Engineerabot/Cheetah/modelio/Raza/doc/hi/img/c8a9e4ff-c5fc-48f4-94d7-1af237ac6b6f.png

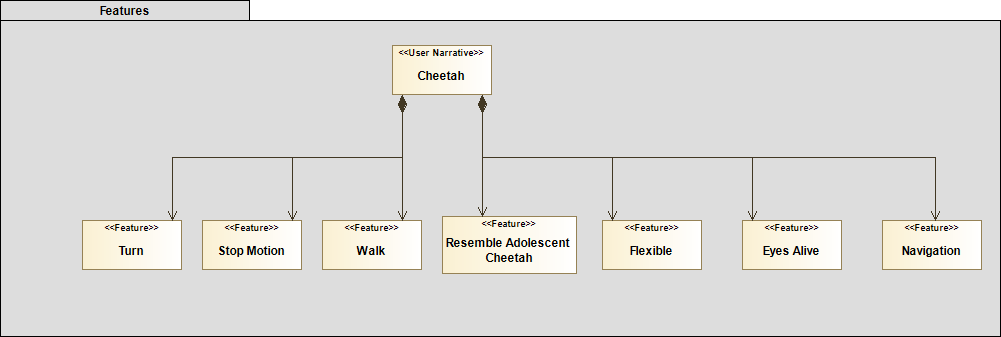
modelio/Raza/doc/hi/img/c8a9e4ff-c5fc-48f4-94d7-1af237ac6b6f.png
