Engineerabot/Cheetah/modelio/Raza/doc/structure/img/92a80e28-67f9-4ed8-8f8e-a8a12a4f9ef7.png

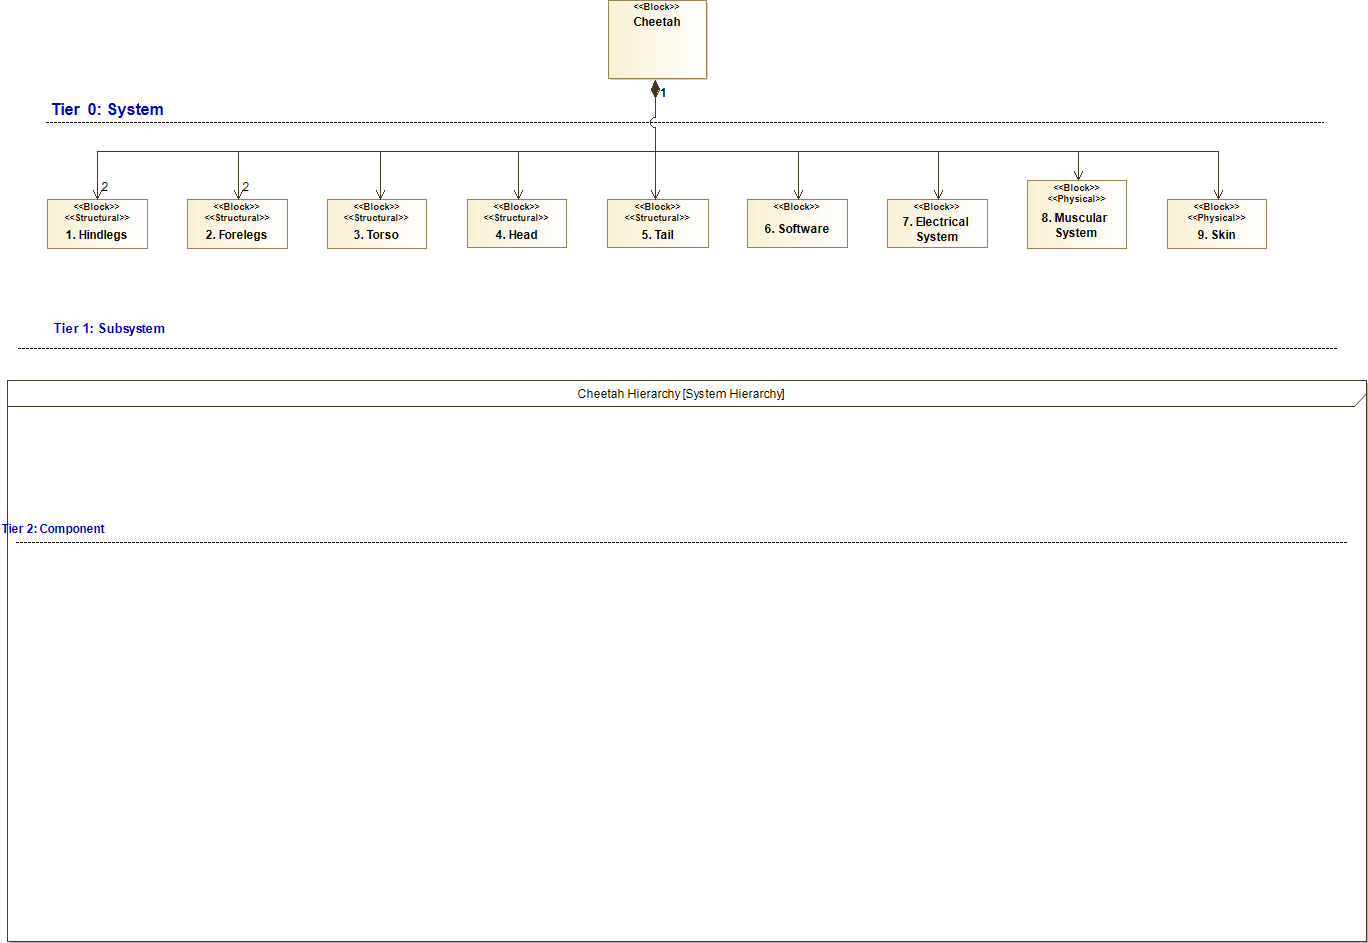
modelio/Raza/doc/structure/img/92a80e28-67f9-4ed8-8f8e-a8a12a4f9ef7.png
