Engineerabot/Cheetah/modelio/Raza/doc/structure/img/a2c1a67e-7b9c-40e4-80ca-a07e13e1c975.png

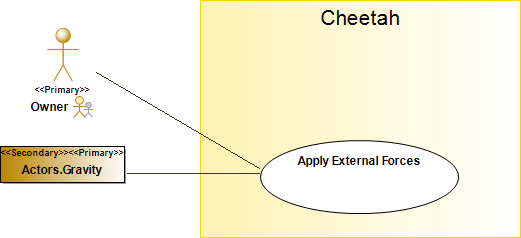
modelio/Raza/doc/structure/img/a2c1a67e-7b9c-40e4-80ca-a07e13e1c975.png
