Engineerabot/Cheetah/manucture/STL/Outer Knee Joint - Left.STL

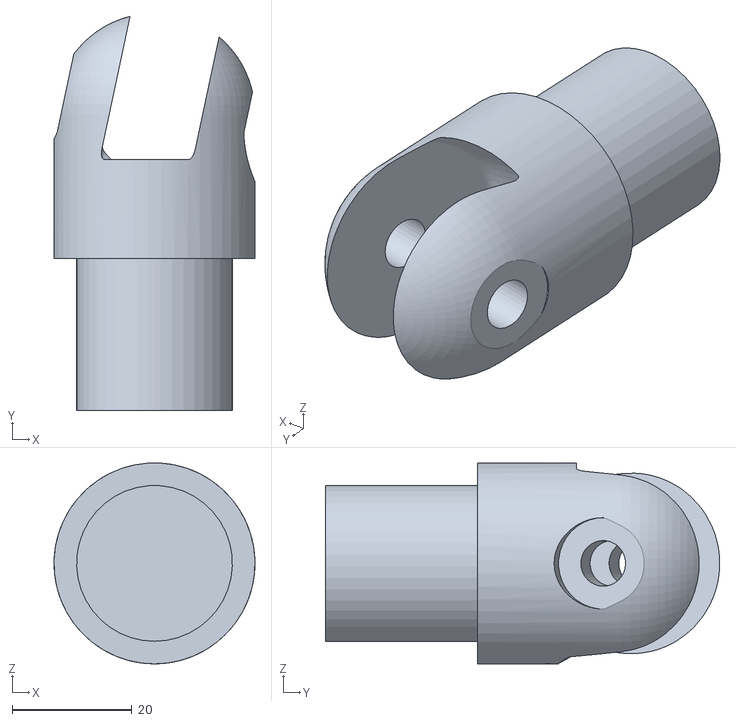
[picture p23: CAD file, 2023-09-10]
manucture/STL/Outer Knee Joint - Left.STL
33.5 x 65.8 x 33.5
