Engineerabot/Cheetah/design/Level 4/Knee Joint Pad.SLDPRT

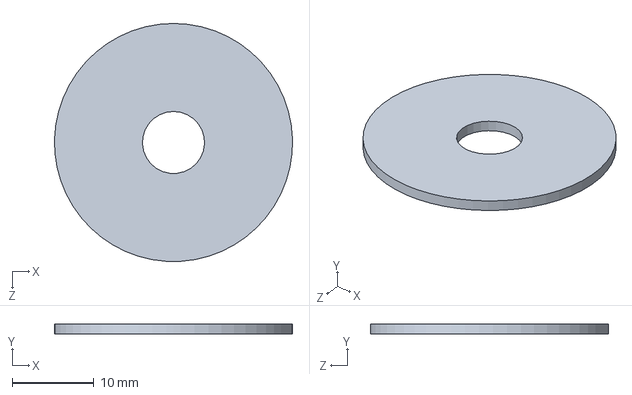
[picture p24: CAD file, 2023-09-10]
design/Level 4/Knee Joint Pad.SLDPRT
29.2 x 1.27 x 29.2 mm
