Engineerabot/Cheetah/manucture/STL/Inner Torso Joint.STL

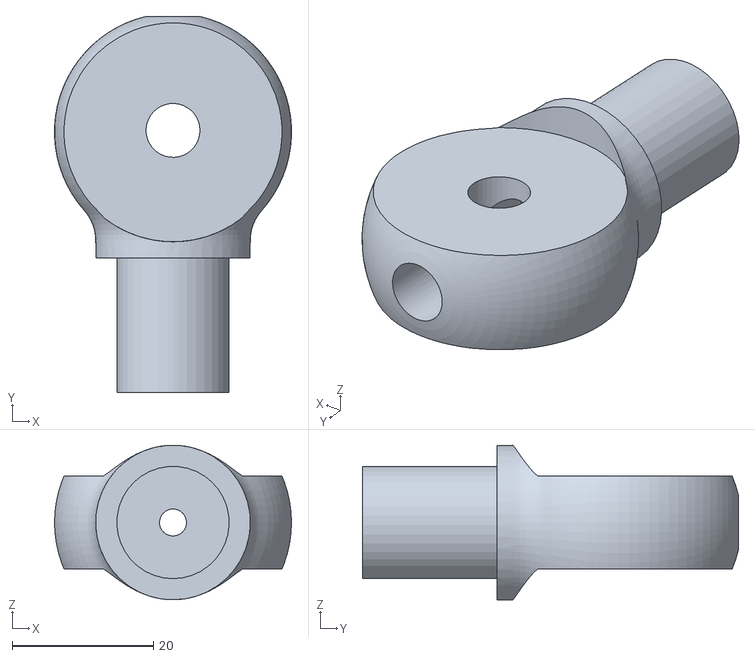
[picture p25: CAD file, 2023-09-10]
manucture/STL/Inner Torso Joint.STL
33.5 x 53.2 x 21.8
