Engineerabot/Cheetah/design/Level 4/Rib7.SLDPRT

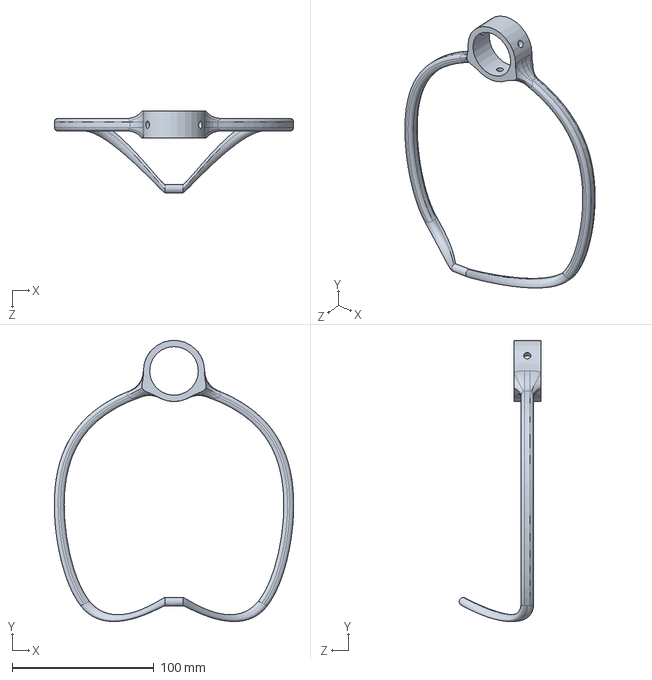
[picture p26: CAD file, 2023-09-10]
design/Level 4/Rib7.SLDPRT
168.7 x 198.0 x 57.5 mm
