Engineerabot/Cheetah/manucture/STL/Outer Elbow Joint.STL

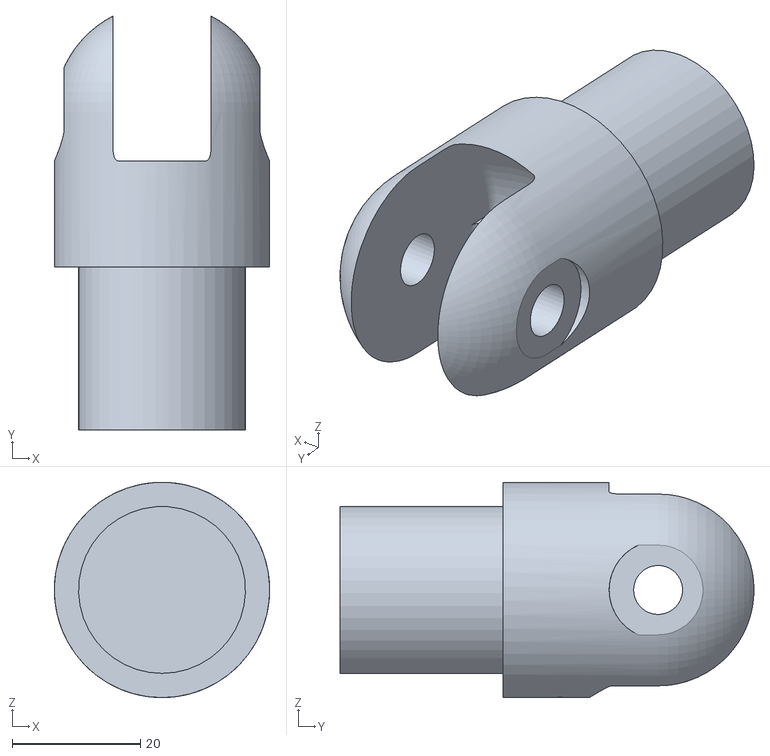
[picture p27: CAD file, 2023-09-10]
manucture/STL/Outer Elbow Joint.STL
33.5 x 64.5 x 33.5
