Engineerabot/Cheetah/design/Level 5/1302-0032-0025-motor mount.SLDPRT

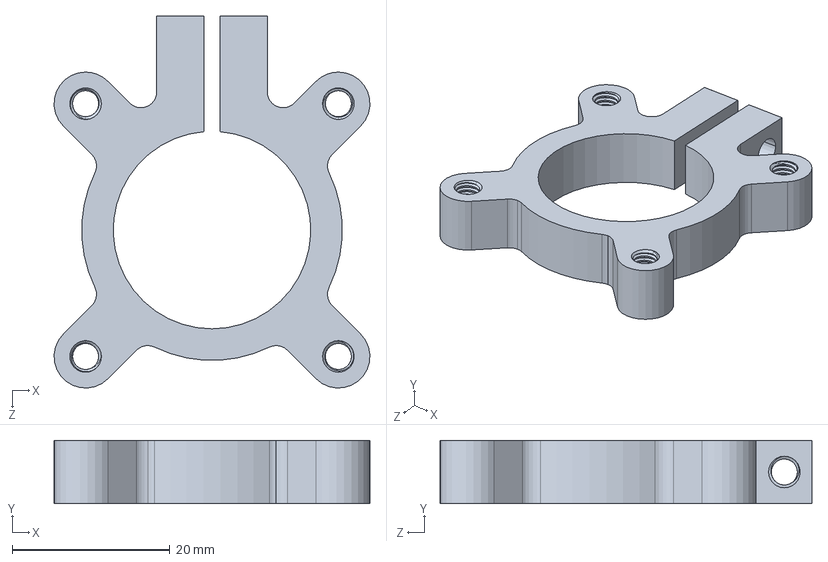
[picture p28: CAD file, 2023-09-10]
design/Level 5/1302-0032-0025-motor mount.SLDPRT
40.0 x 8.00 x 47.1 mm
