Engineerabot/Cheetah/manucture/STL/Inner Knee Joint.STL

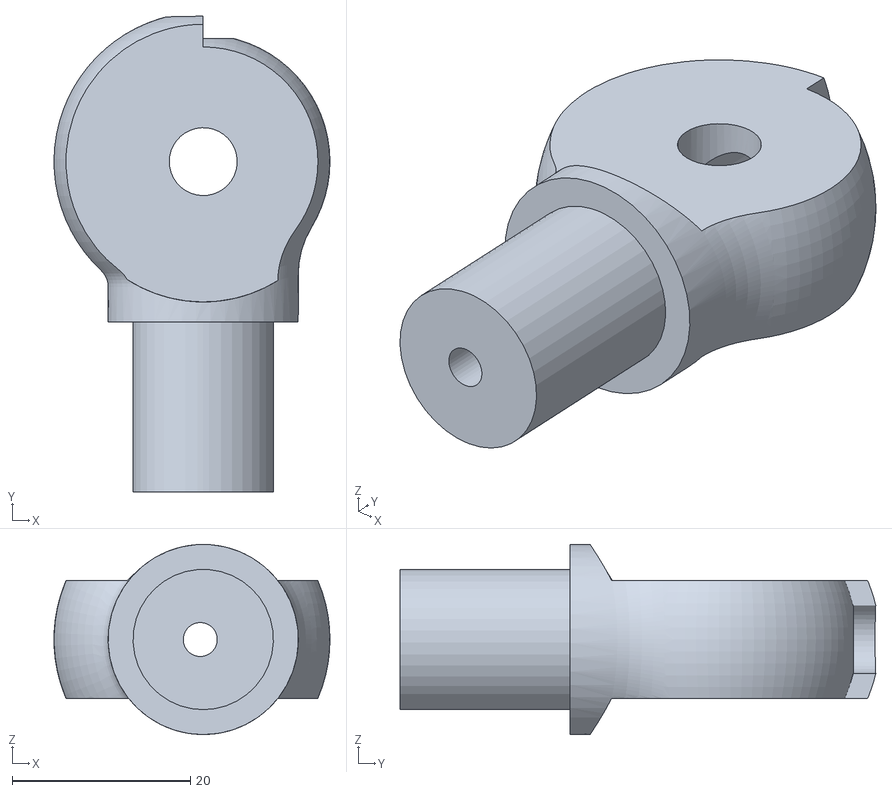
[picture p29: CAD file, 2022-10-15]
manucture/STL/Inner Knee Joint.STL
31.0 x 53.4 x 21.3
