Engineerabot/Cheetah/design/Level 5/Rotary Softpot.SLDPRT

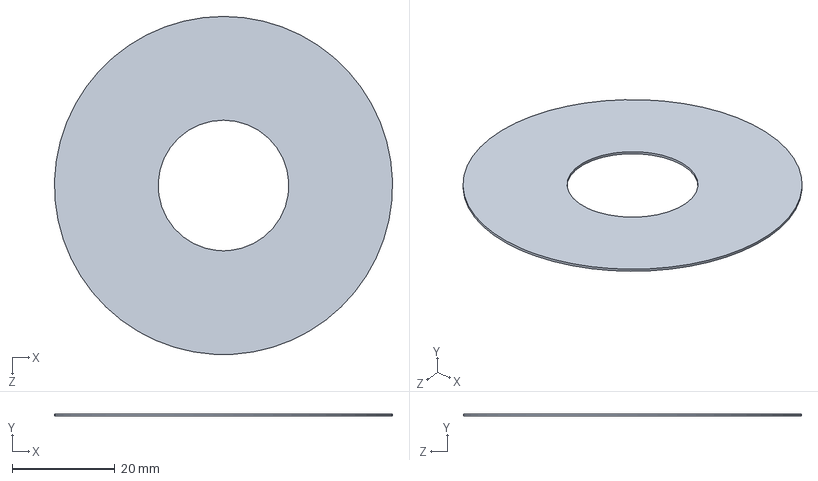
[picture p30: CAD file, 2023-09-10]
design/Level 5/Rotary Softpot.SLDPRT
65.7 x 0.457 x 65.7 mm
