Engineerabot/Cheetah/design/Level 4/Pelvis Connector.SLDPRT

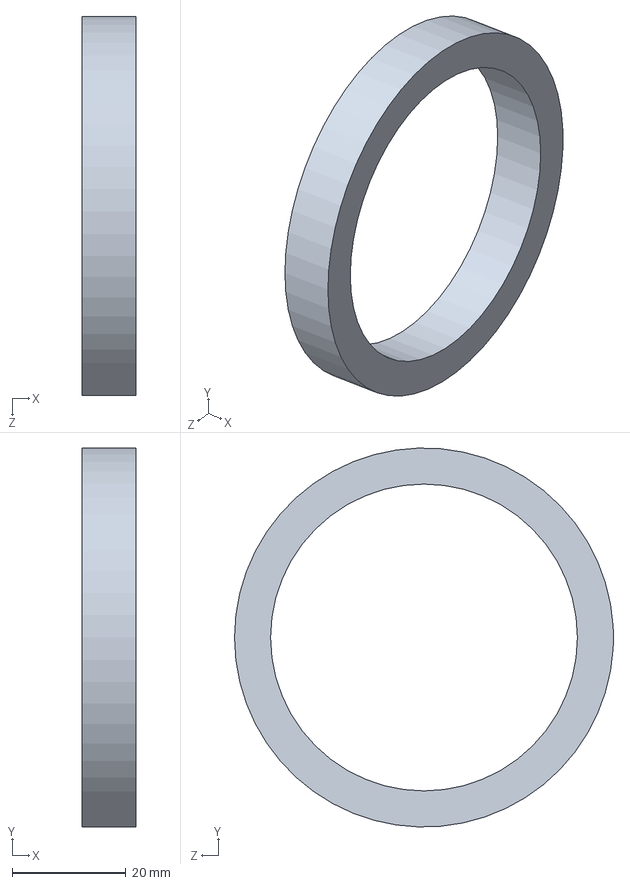
[picture p31: CAD file, 2023-09-10]
design/Level 4/Pelvis Connector.SLDPRT
9.53 x 66.6 x 66.7 mm
