Engineerabot/Cheetah/manucture/STL/Hip Cap.STL

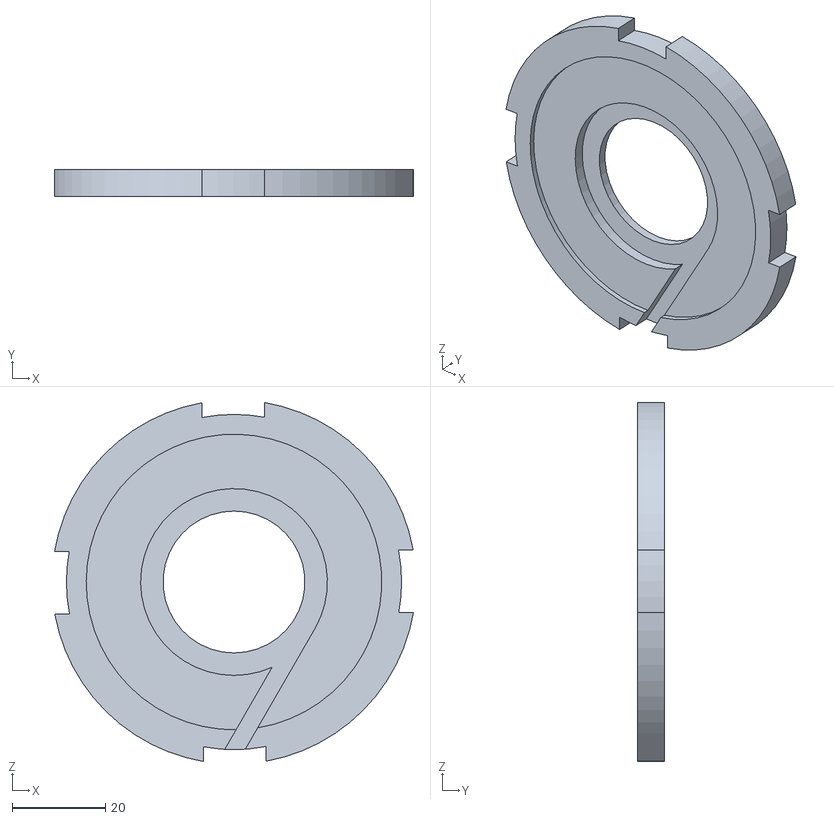
[picture p32: CAD file, 2022-10-13]
manucture/STL/Hip Cap.STL
77.1 x 5.84 x 77.1
