Engineerabot/Cheetah/design/Level 4/TorsionShaft.SLDPRT

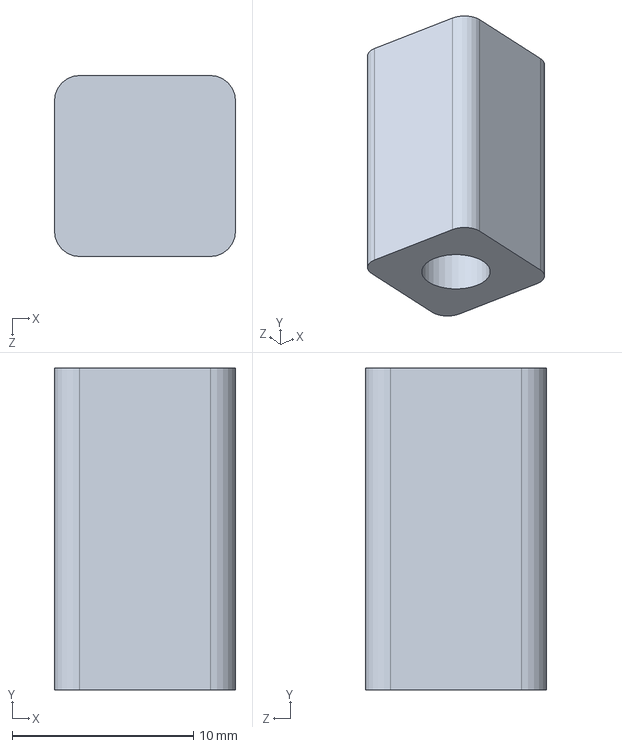
[picture p33: CAD file, 2023-09-10]
design/Level 4/TorsionShaft.SLDPRT
10.0 x 17.8 x 10.0 mm
