Engineerabot/Cheetah/design/Level 5/6910-2RS-EZO.SLDPRT

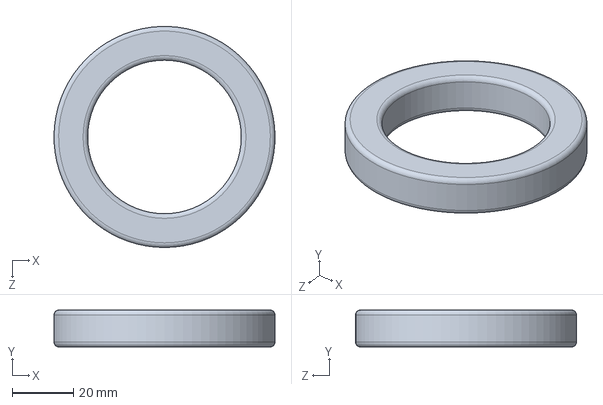
[picture p34: CAD file, 2023-09-10]
design/Level 5/6910-2RS-EZO.SLDPRT
72.0 x 12.0 x 72.0 mm
