Engineerabot/Cheetah/manucture/STL/Outer Hip Joint.STL

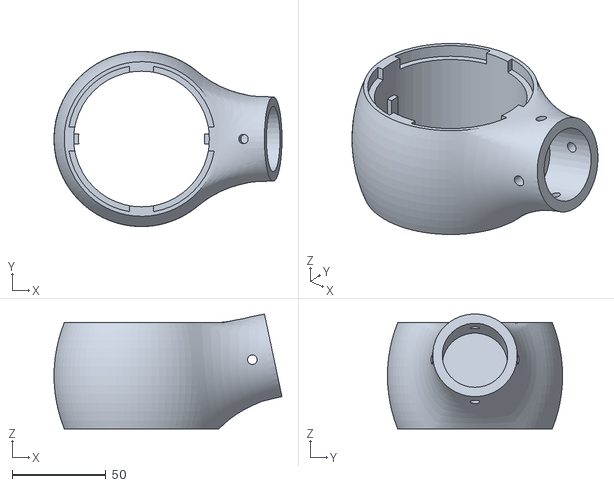
[picture p35: CAD file, 2022-10-13]
manucture/STL/Outer Hip Joint.STL
121.9 x 93.6 x 61.5
