Engineerabot/Cheetah/manucture/STL/Inner Hip Joint.STL

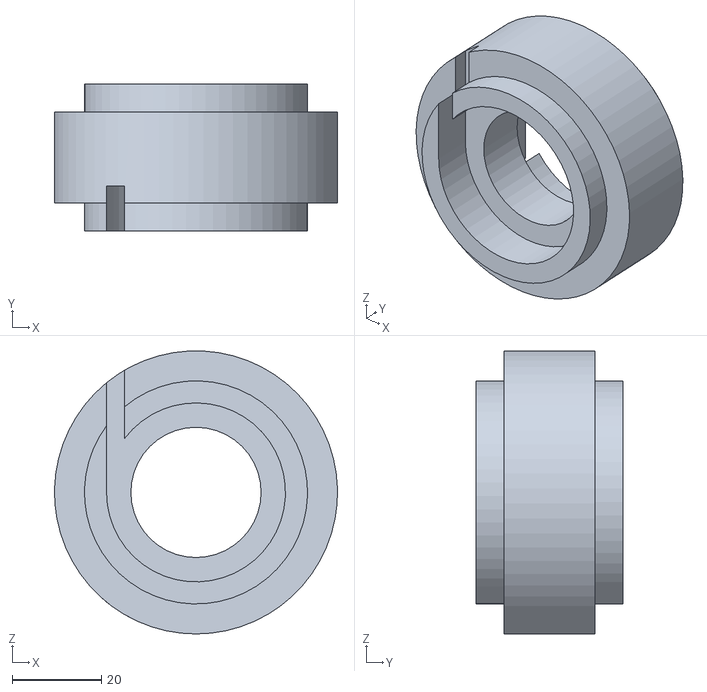
[picture p36: CAD file, 2022-10-13]
manucture/STL/Inner Hip Joint.STL
63.5 x 33.0 x 63.5
