Engineerabot/Cheetah/design/Level 4/Rib12.SLDPRT

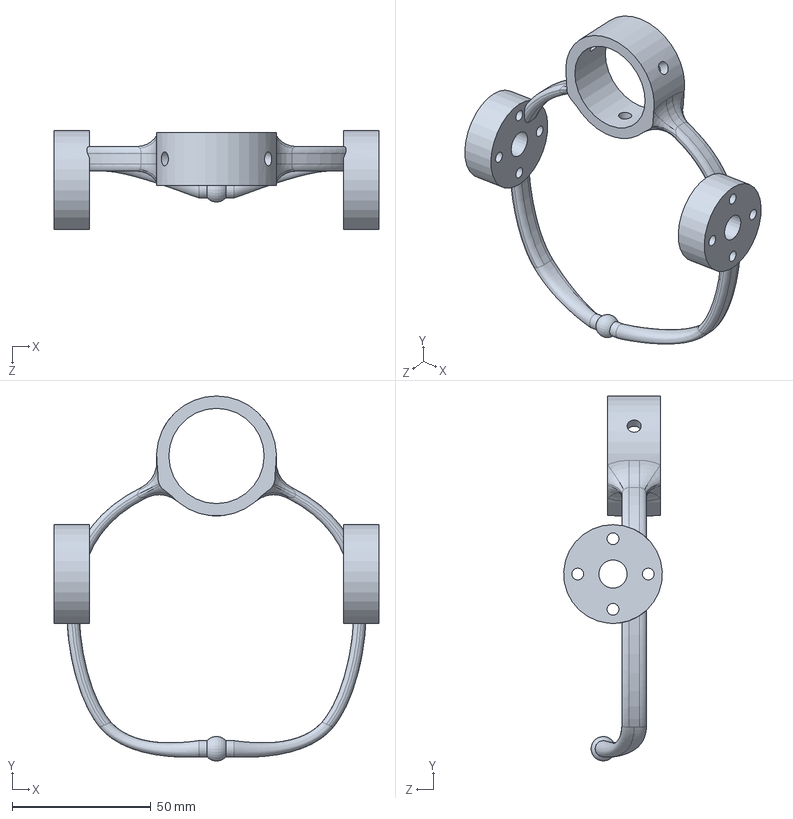
[picture p37: CAD file, 2023-09-10]
design/Level 4/Rib12.SLDPRT
116.8 x 131.4 x 35.5 mm
