Engineerabot/Cheetah/manucture/STL/Scapula - Right.STL

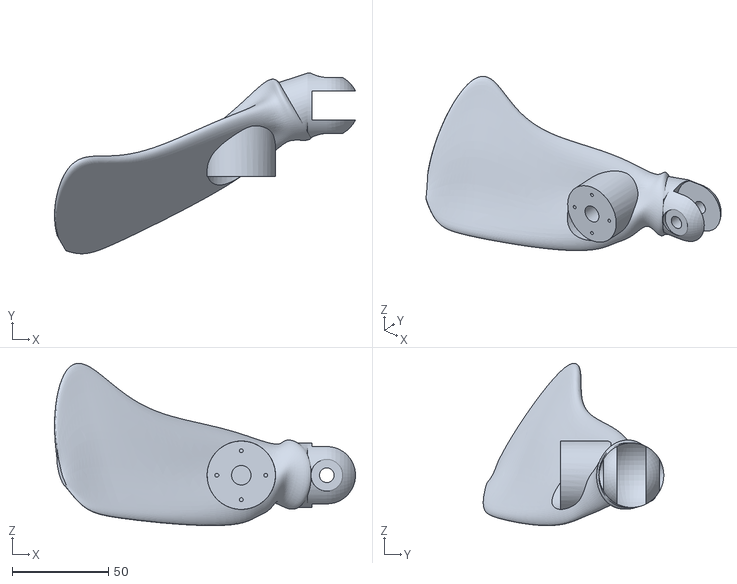
[picture p38: CAD file, 2022-10-08]
manucture/STL/Scapula - Right.STL
156.5 x 93.9 x 84.3
