Engineerabot/Cheetah/design/Level 4/Femur.SLDPRT

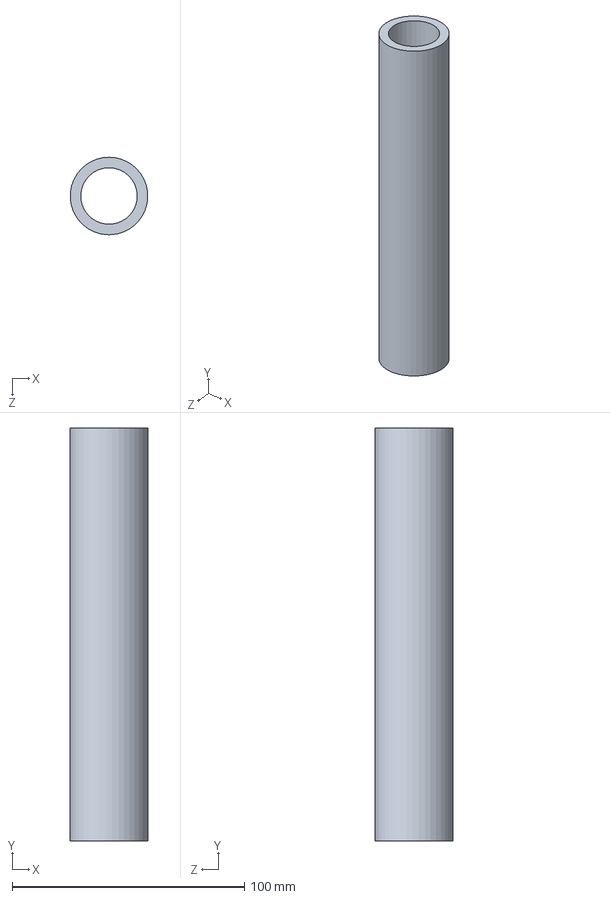
[picture p39: CAD file, 2023-09-10]
design/Level 4/Femur.SLDPRT
33.4 x 177.8 x 33.4 mm
