Engineerabot/Cheetah/manucture/STL/Outer Torso Joint.STL

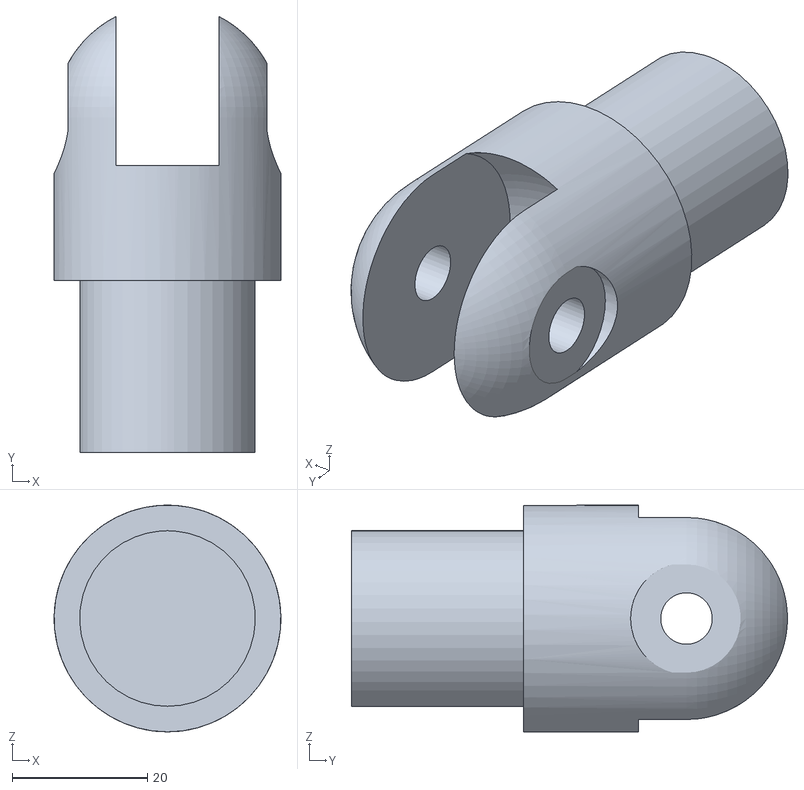
[picture p40: CAD file, 2022-10-08]
manucture/STL/Outer Torso Joint.STL
33.5 x 64.5 x 33.5
