Engineerabot/Cheetah/design/Level 4/Rib2.SLDPRT

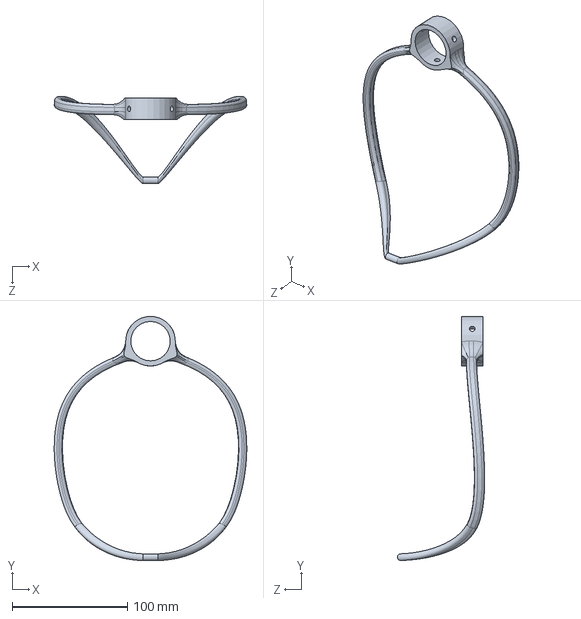
[picture p41: CAD file, 2023-09-10]
design/Level 4/Rib2.SLDPRT
167.4 x 212.1 x 75.9 mm
