Engineerabot/Cheetah/manucture/STL/Skull Top.STL

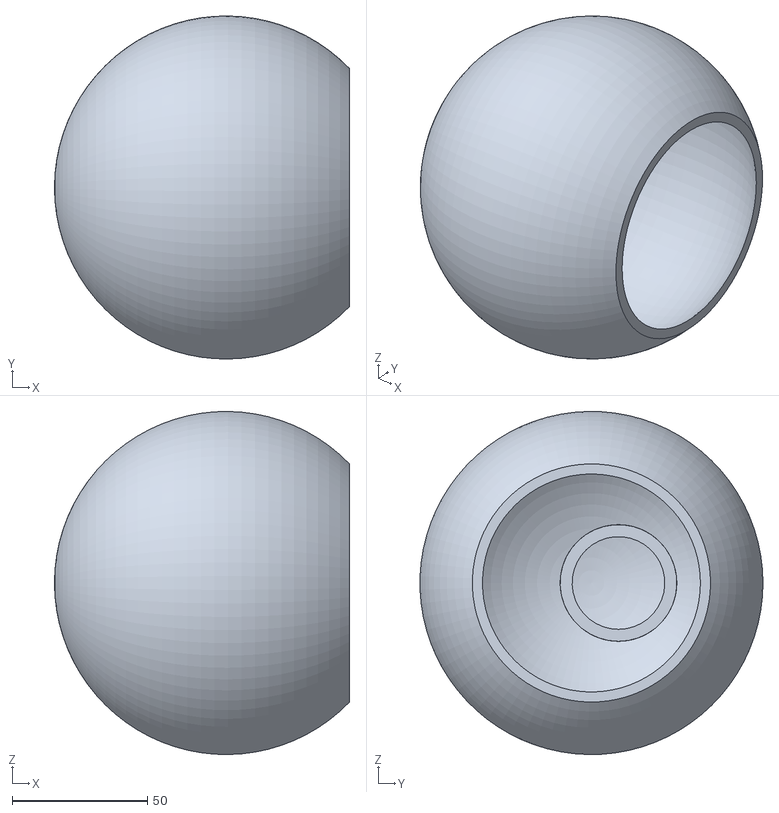
[picture p42: CAD file, 2022-10-08]
manucture/STL/Skull Top.STL
109.2 x 126.9 x 127.0
