Engineerabot/Cheetah/design/Level 4/Upper Right Knee.SLDPRT

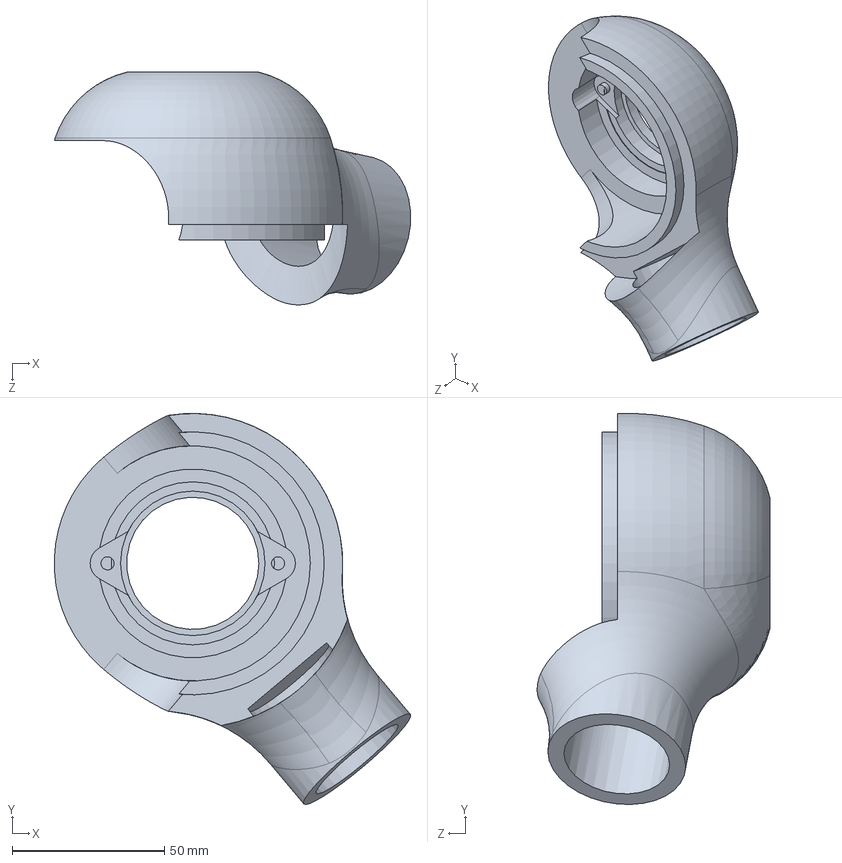
[picture p43: CAD file, 2023-09-10]
design/Level 4/Upper Right Knee.SLDPRT
117.0 x 128.4 x 76.4 mm
