Engineerabot/Cheetah/manucture/STL/Pelvis.STL

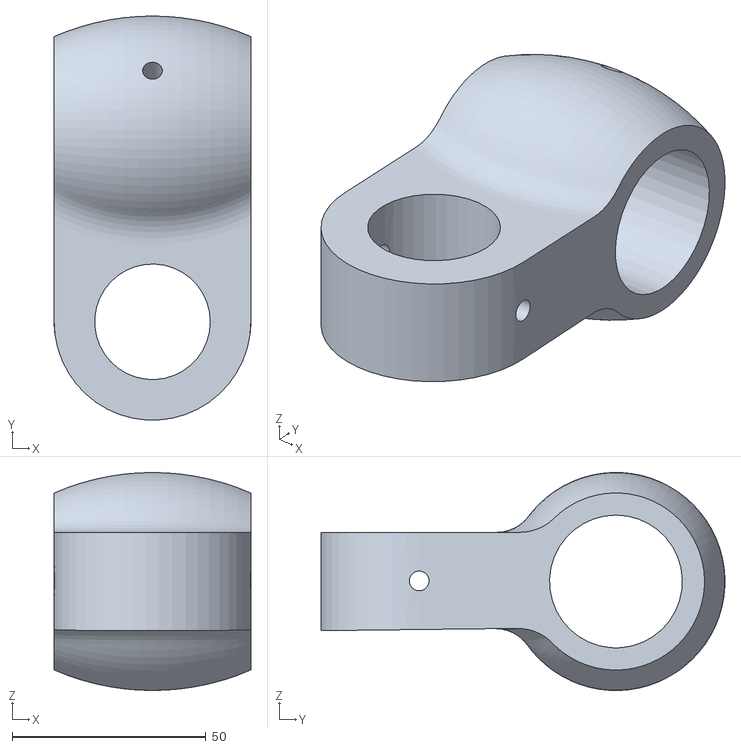
[picture p44: CAD file, 2022-10-08]
manucture/STL/Pelvis.STL
50.8 x 104.3 x 56.3
