Engineerabot/Cheetah/design/Level 4/Rib9.SLDPRT

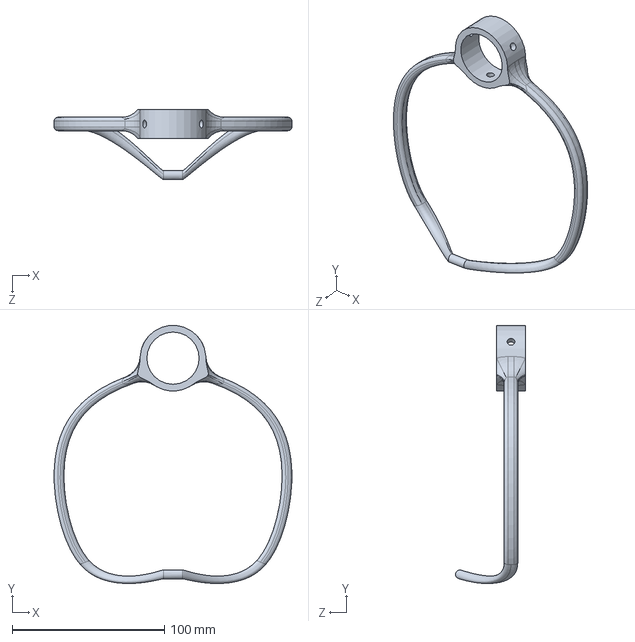
[picture p45: CAD file, 2023-09-10]
design/Level 4/Rib9.SLDPRT
156.1 x 169.4 x 46.0 mm
