Engineerabot/Cheetah/design/Level 5/6908-2RS-EZO.SLDPRT

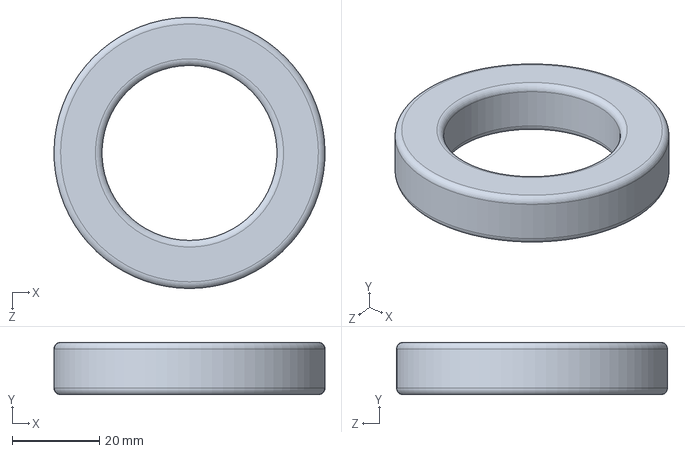
[picture p46: CAD file, 2023-09-10]
design/Level 5/6908-2RS-EZO.SLDPRT
62.0 x 12.0 x 62.0 mm
