Engineerabot/Cheetah/design/Level 4/Outer Knee Cap.SLDPRT

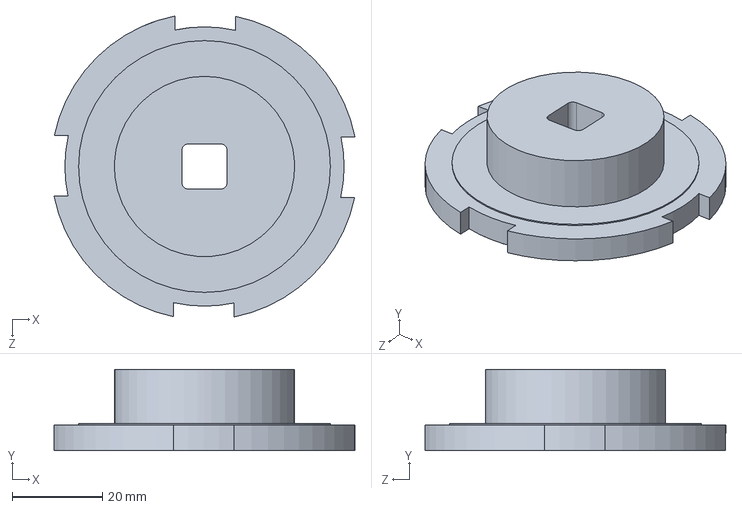
[picture p47: CAD file, 2023-09-10]
design/Level 4/Outer Knee Cap.SLDPRT
66.8 x 18.1 x 66.8 mm
