Engineerabot/Cheetah/design/Level 5/32 RPM Premium Gear Motor.SLDPRT

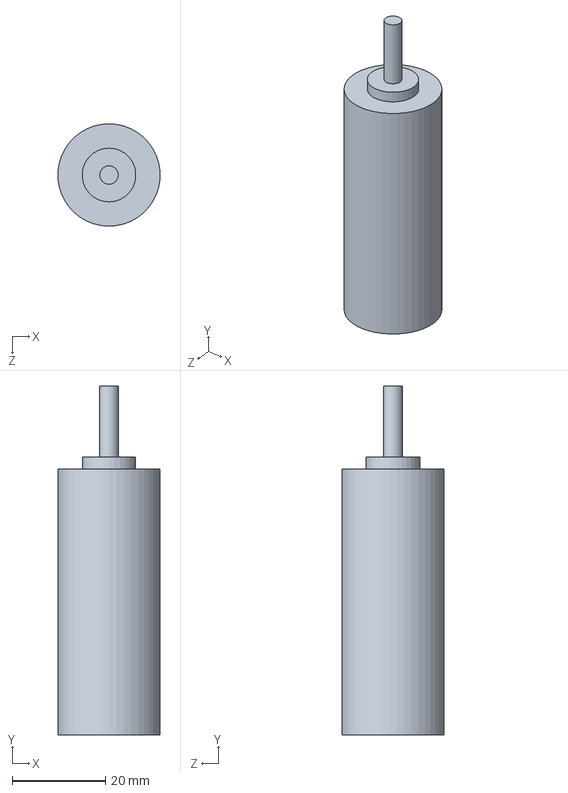
[picture p48: CAD file, 2023-09-10]
design/Level 5/32 RPM Premium Gear Motor.SLDPRT
21.9 x 75.0 x 22.0 mm
