Engineerabot/Cheetah/manucture/STL/Skull.STL

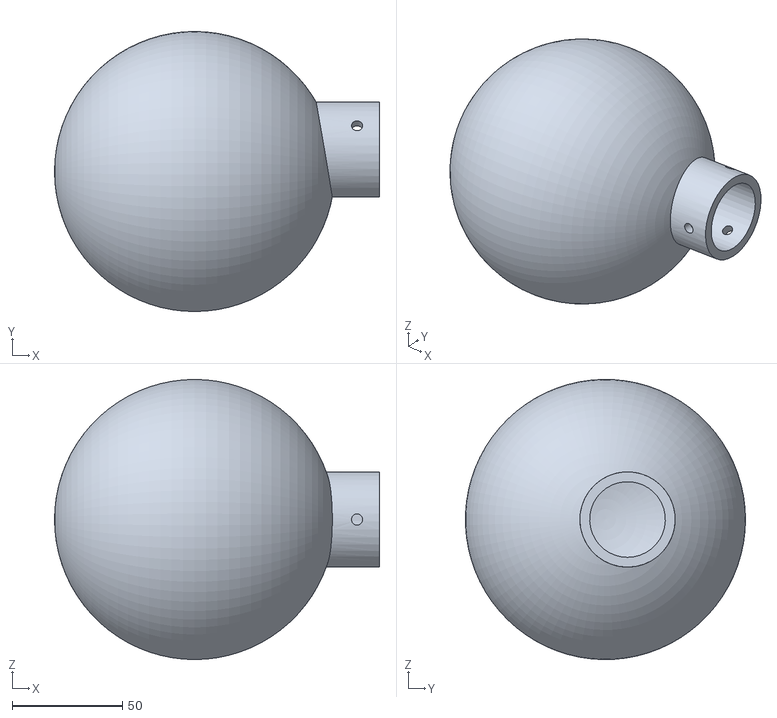
[picture p49: CAD file, 2022-10-08]
manucture/STL/Skull.STL
147.3 x 126.9 x 127.0
