Engineerabot/Cheetah/design/Level 5/PT112-1132-5125-MW-LH-4000-N-IN Torsion Spring.SLDPRT

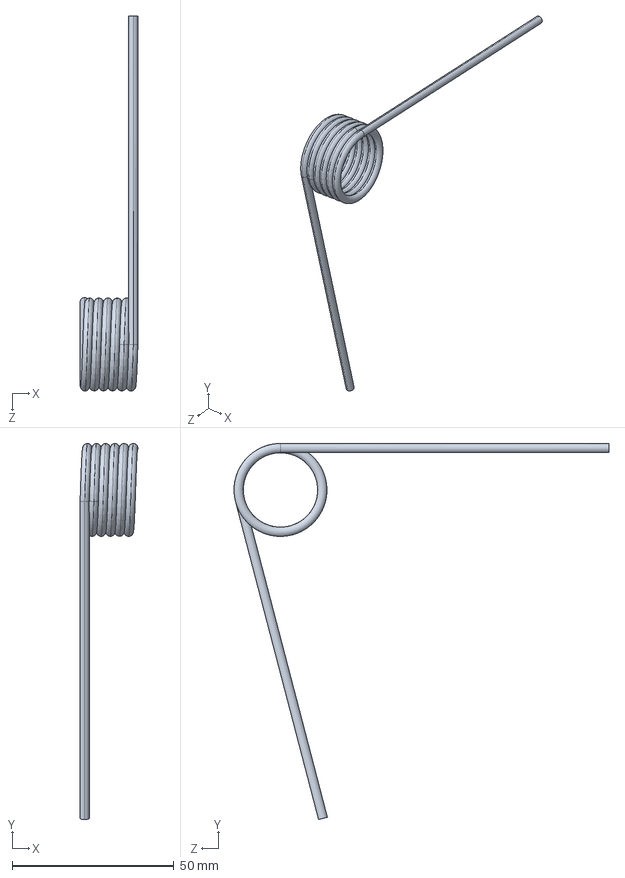
[picture p50: CAD file, 2023-09-10]
design/Level 5/PT112-1132-5125-MW-LH-4000-N-IN Torsion Spring.SLDPRT
17.9 x 116.3 x 116.0 mm
