Engineerabot/Cheetah/manucture/STL/Inner Neck Joint.STL

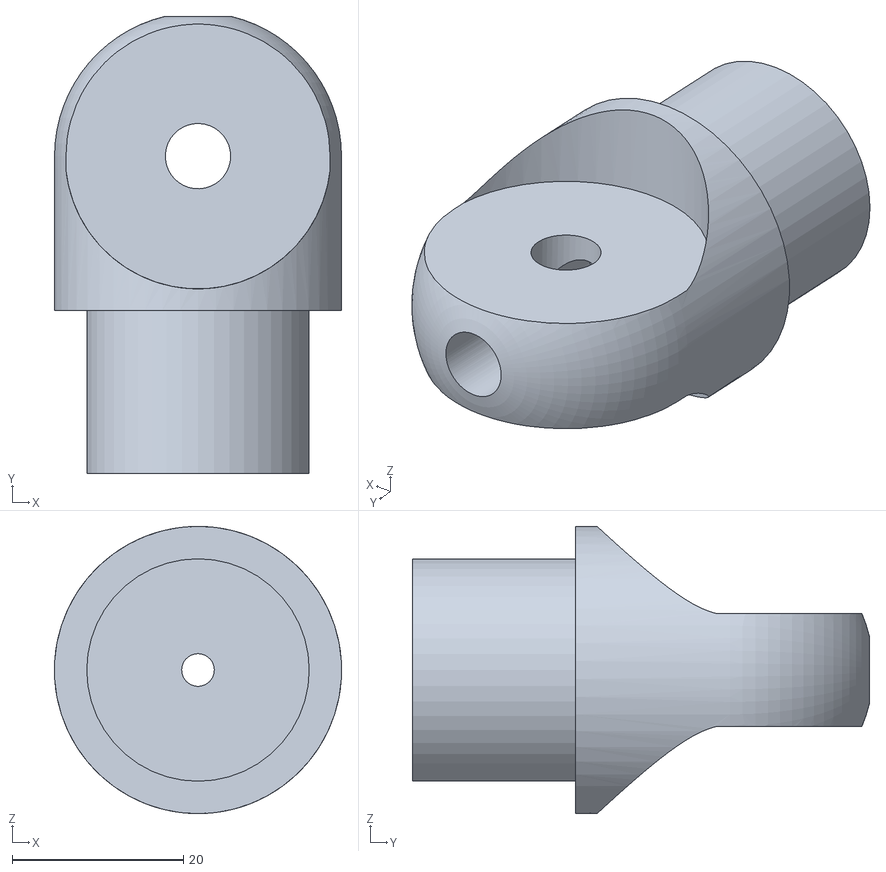
[picture p51: CAD file, 2022-10-08]
manucture/STL/Inner Neck Joint.STL
33.5 x 53.4 x 33.5
