Engineerabot/Cheetah/design/Level 4/Hip Cap.SLDPRT

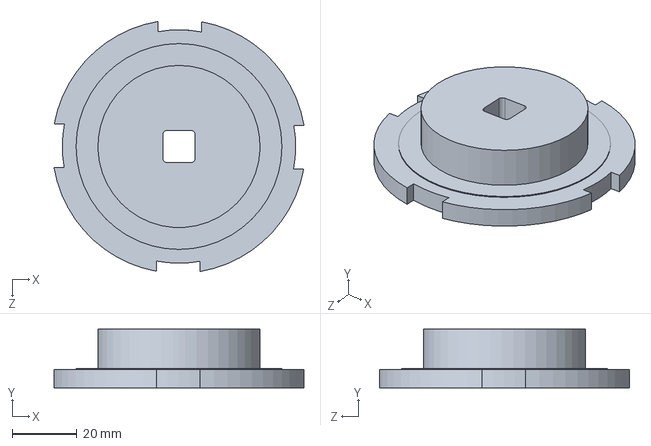
[picture p52: CAD file, 2023-09-10]
design/Level 4/Hip Cap.SLDPRT
77.1 x 18.1 x 77.1 mm
