Engineerabot/Cheetah/design/Level 5/43 RPM Econ Gear Motor.SLDPRT

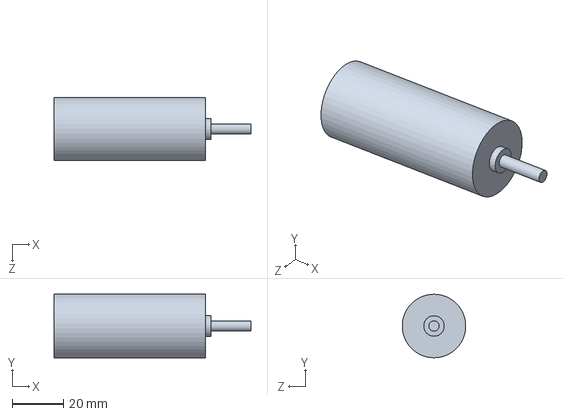
[picture p53: CAD file, 2023-09-10]
design/Level 5/43 RPM Econ Gear Motor.SLDPRT
76.8 x 24.8 x 24.7 mm
