Engineerabot/Cheetah/design/Level 4/Rib8.SLDPRT

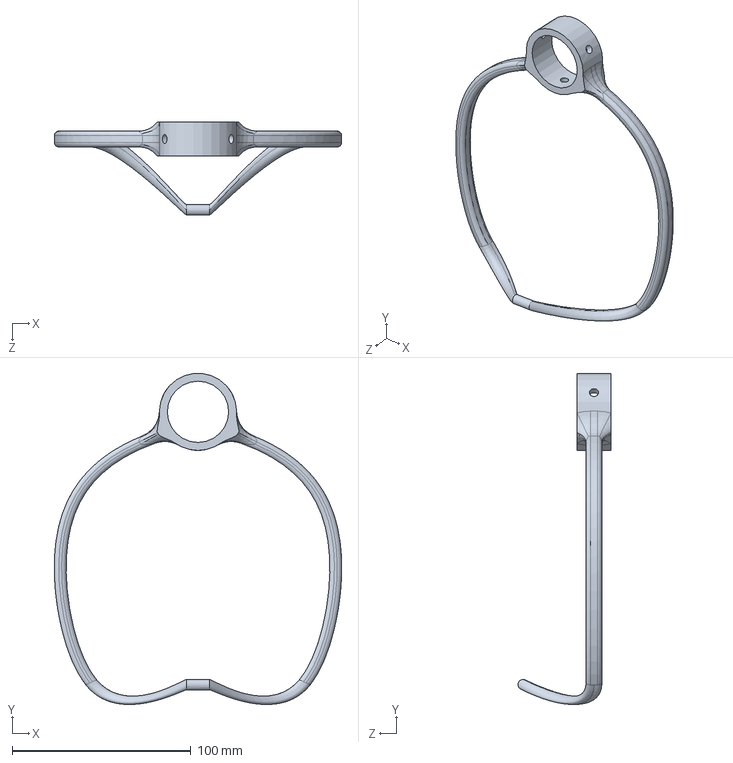
[picture p54: CAD file, 2023-09-10]
design/Level 4/Rib8.SLDPRT
160.8 x 185.2 x 52.0 mm
