Engineerabot/Cheetah/design/Level 4/Inner Hip Cap.SLDPRT

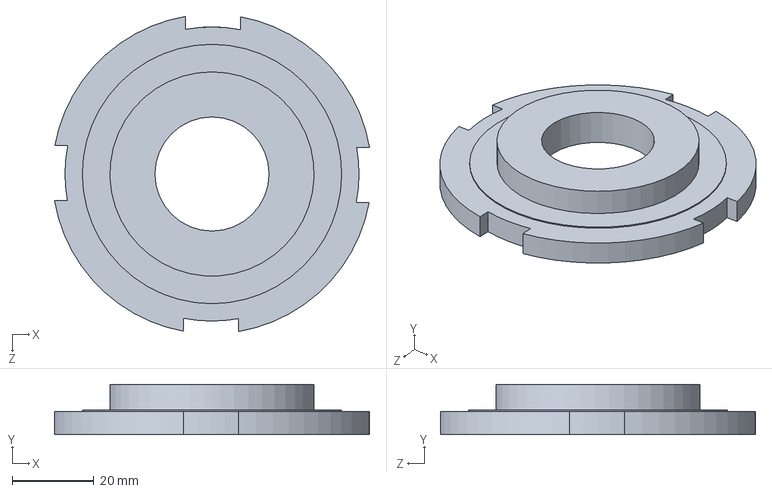
[picture p55: CAD file, 2023-09-10]
design/Level 4/Inner Hip Cap.SLDPRT
77.1 x 12.4 x 77.1 mm
