Engineerabot/Cheetah/design/Level 4/Upper Left Pelvis.SLDPRT

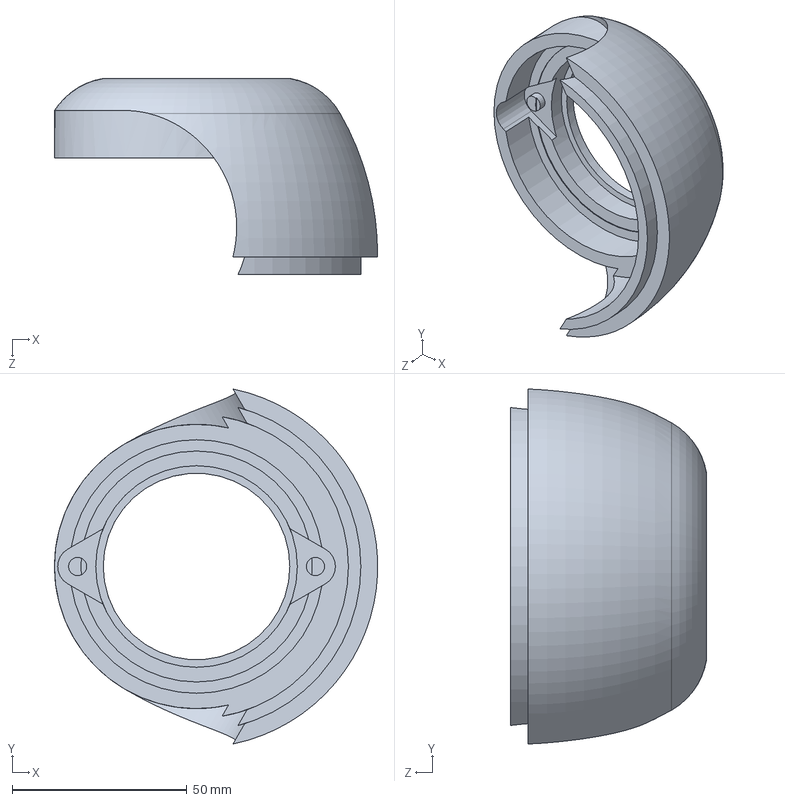
[picture p56: CAD file, 2023-09-10]
design/Level 4/Upper Left Pelvis.SLDPRT
92.4 x 101.5 x 56.1 mm
