Engineerabot/Cheetah/design/Level 4/KneeShaftCollar.SLDPRT

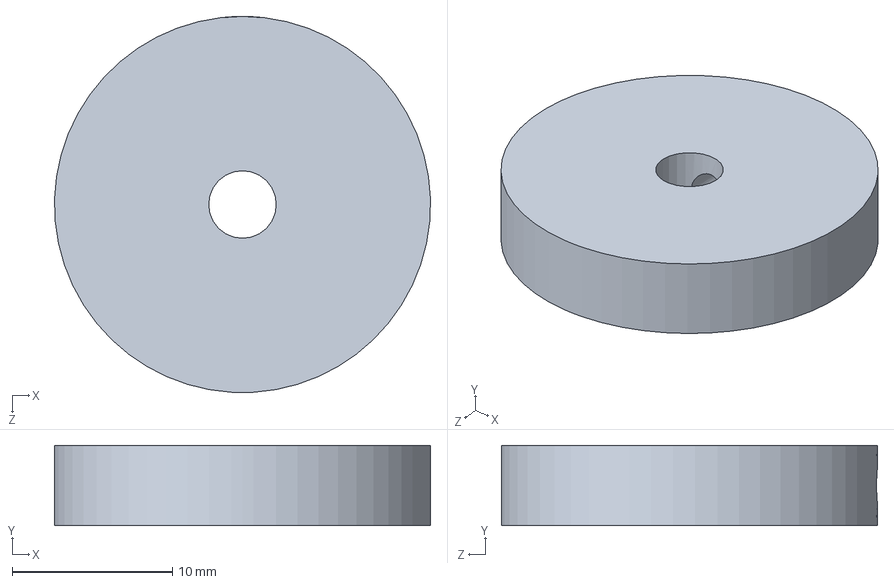
[picture p57: CAD file, 2023-09-10]
design/Level 4/KneeShaftCollar.SLDPRT
23.5 x 5.00 x 23.5 mm
