Engineerabot/Cheetah/design/Level 4/Radius.SLDPRT

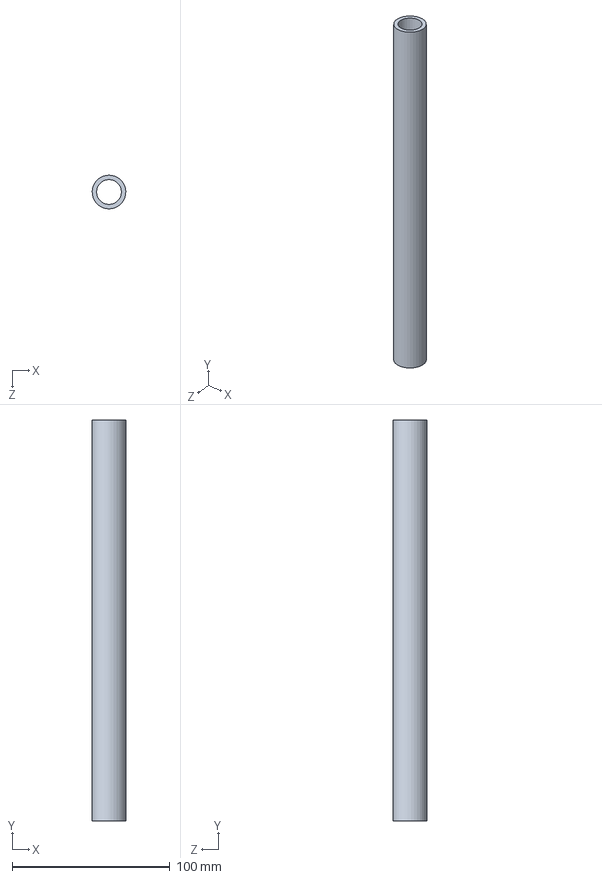
[picture p58: CAD file, 2023-09-10]
design/Level 4/Radius.SLDPRT
21.3 x 254.0 x 21.3 mm
