Engineerabot/Cheetah/design/Level 4/Inner Pelvis Cap.SLDPRT

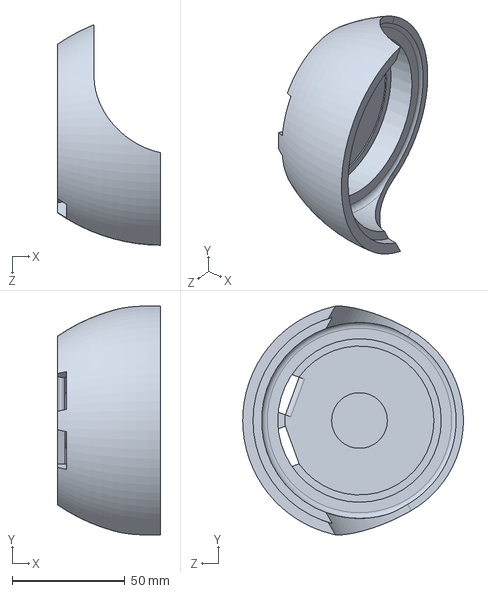
[picture p59: CAD file, 2023-09-10]
design/Level 4/Inner Pelvis Cap.SLDPRT
45.7 x 101.6 x 97.9 mm
