Engineerabot/Cheetah/design/Level 4/Hip Bar.SLDPRT

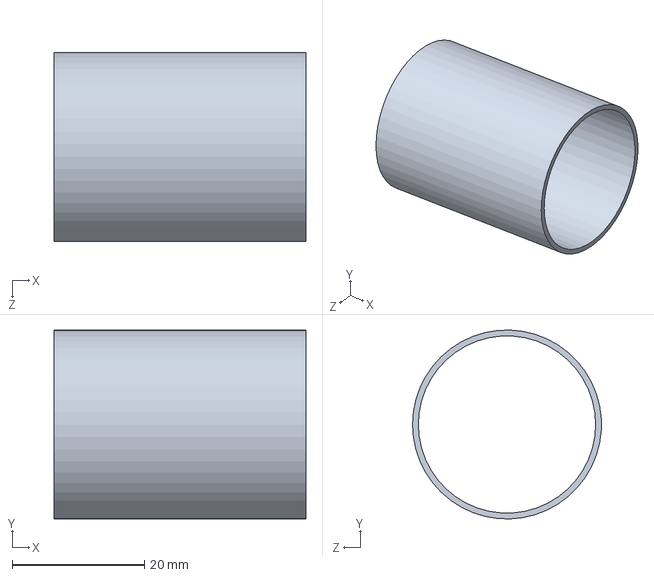
[picture p60: CAD file, 2023-09-10]
design/Level 4/Hip Bar.SLDPRT
38.1 x 28.6 x 28.6 mm
