Engineerabot/Cheetah/design/Level 4/InnerCapRadius.SLDPRT

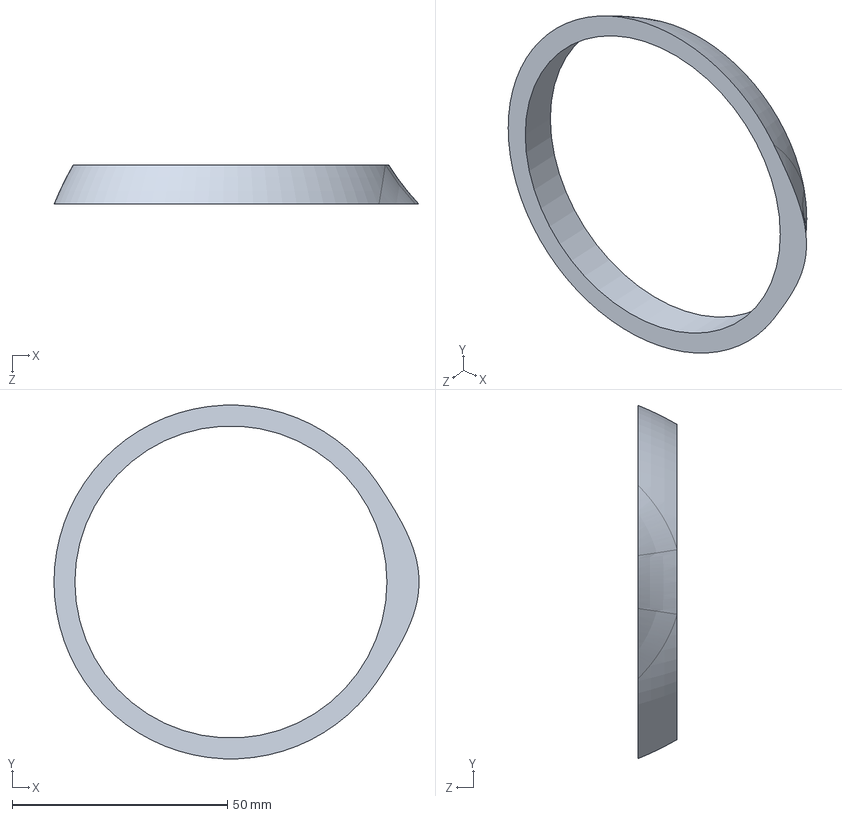
[picture p61: CAD file, 2023-09-10]
design/Level 4/InnerCapRadius.SLDPRT
84.8 x 82.2 x 9.14 mm
