Engineerabot/Cheetah/design/Level 4/Rib1.SLDPRT

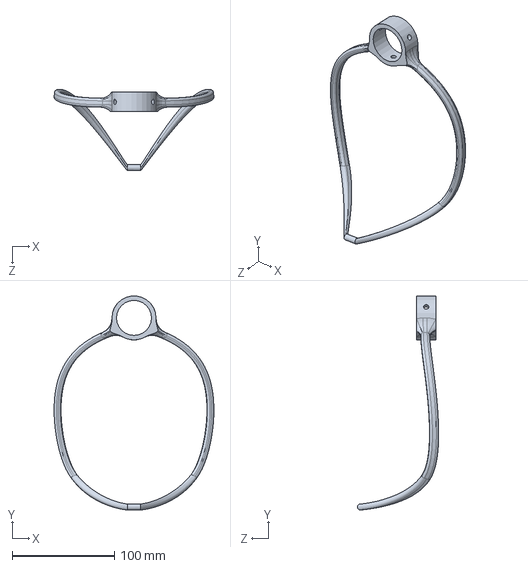
[picture p62: CAD file, 2023-09-10]
design/Level 4/Rib1.SLDPRT
156.5 x 209.5 x 79.7 mm
