Engineerabot/Cheetah/design/Level 4/ShaftCollar.SLDPRT

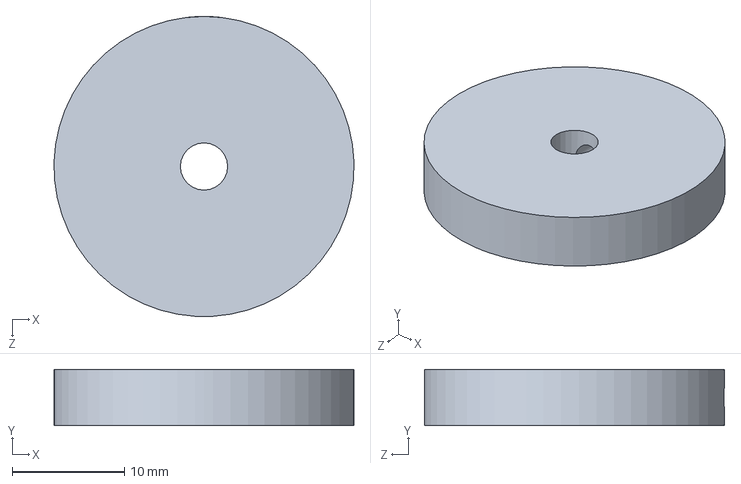
[picture p63: CAD file, 2023-09-10]
design/Level 4/ShaftCollar.SLDPRT
26.8 x 5.00 x 26.8 mm
