Engineerabot/Cheetah/design/Level 4/Rib3.SLDPRT

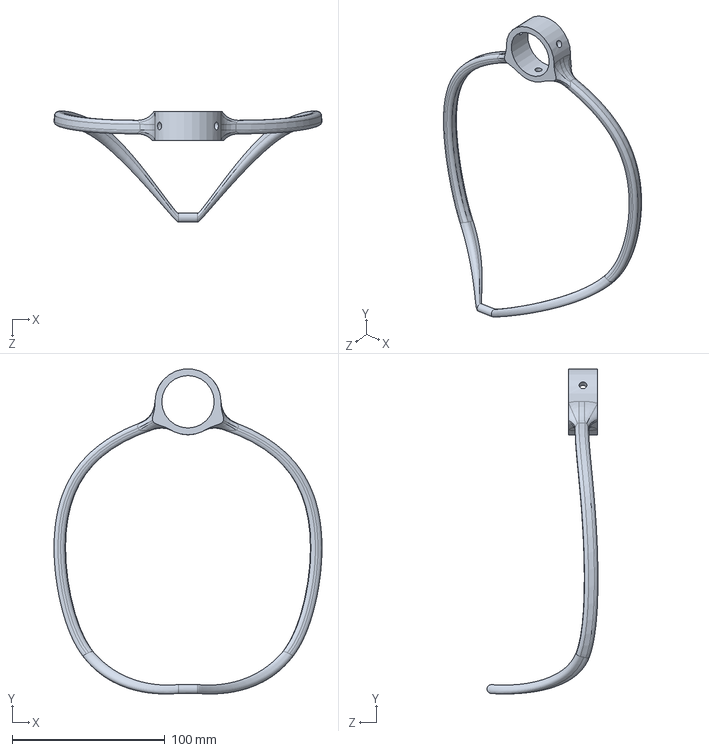
[picture p64: CAD file, 2023-09-10]
design/Level 4/Rib3.SLDPRT
175.2 x 212.5 x 72.6 mm
