Engineerabot/Cheetah/design/Level 4/Pelvis.SLDPRT

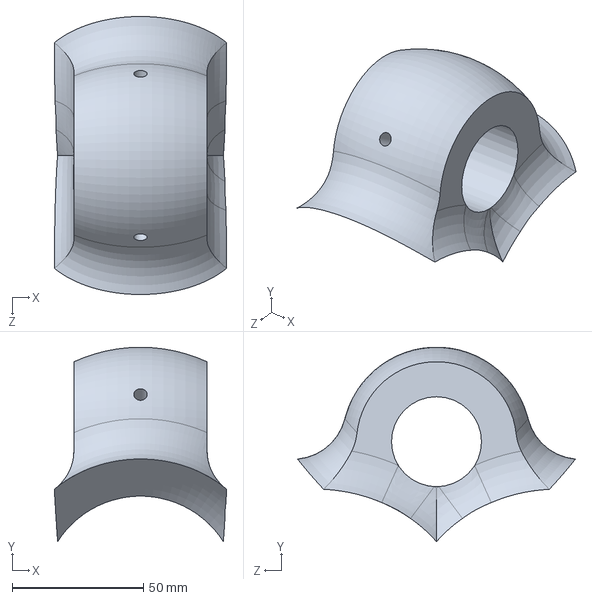
[picture p65: CAD file, 2023-09-10]
design/Level 4/Pelvis.SLDPRT
65.7 x 74.1 x 106.0 mm
