Engineerabot/Cheetah/design/Level 4/Outer Knee Joint.SLDPRT

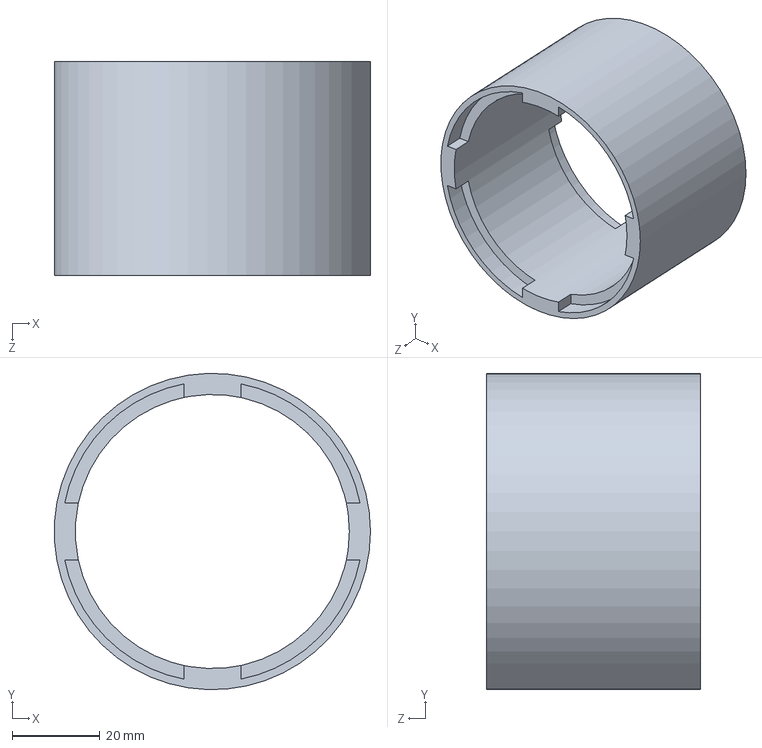
[picture p66: CAD file, 2023-09-10]
design/Level 4/Outer Knee Joint.SLDPRT
72.1 x 72.1 x 48.9 mm
