Engineerabot/Cheetah/design/Level 4/Inner Knee Cap.SLDPRT

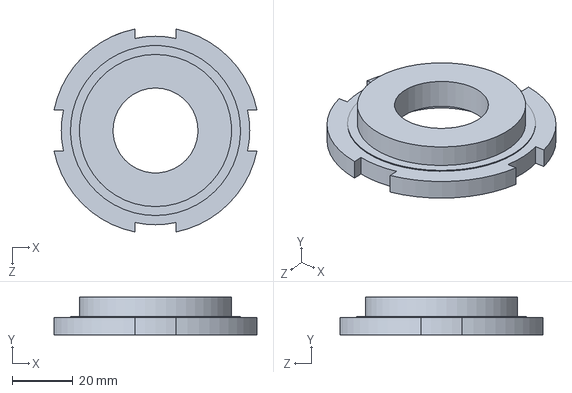
[picture p67: CAD file, 2023-09-10]
design/Level 4/Inner Knee Cap.SLDPRT
66.7 x 12.4 x 66.7 mm
