Engineerabot/Cheetah/design/Level 4/Inner Hip Joint.SLDPRT

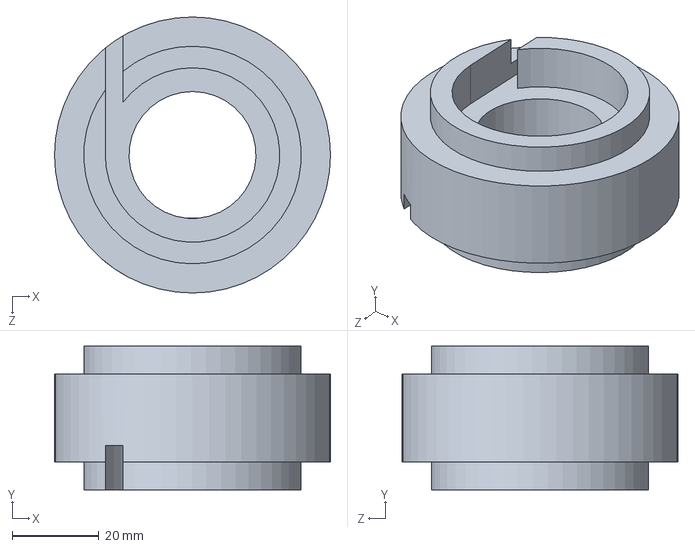
[picture p68: CAD file, 2023-09-10]
design/Level 4/Inner Hip Joint.SLDPRT
63.5 x 33.0 x 63.5 mm
