Engineerabot/Cheetah/design/Level 4/Outer Torso Joint.SLDPRT

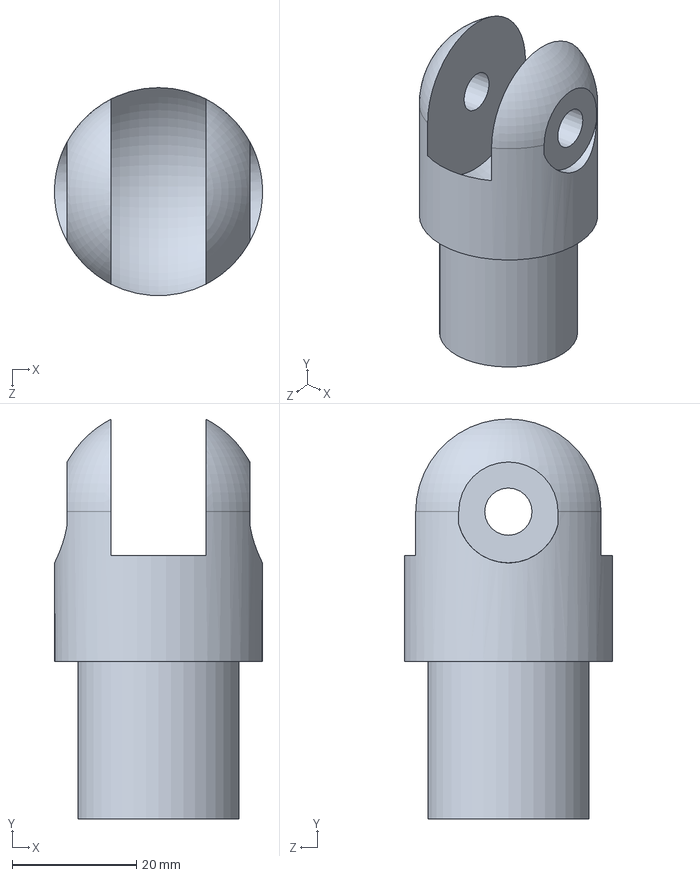
[picture p69: CAD file, 2023-09-10]
design/Level 4/Outer Torso Joint.SLDPRT
33.5 x 64.5 x 33.5 mm
