Engineerabot/Cheetah/design/Level 4/Neck.SLDPRT

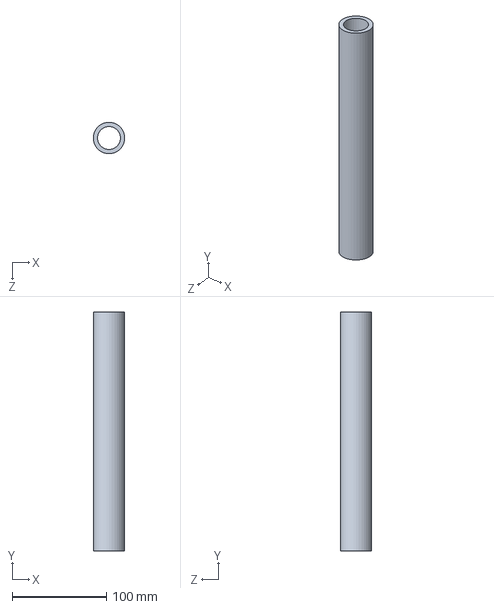
[picture p70: CAD file, 2023-09-10]
design/Level 4/Neck.SLDPRT
33.4 x 254.0 x 33.4 mm
