Engineerabot/Cheetah/design/Level 4/Inner Knee Cover.SLDPRT

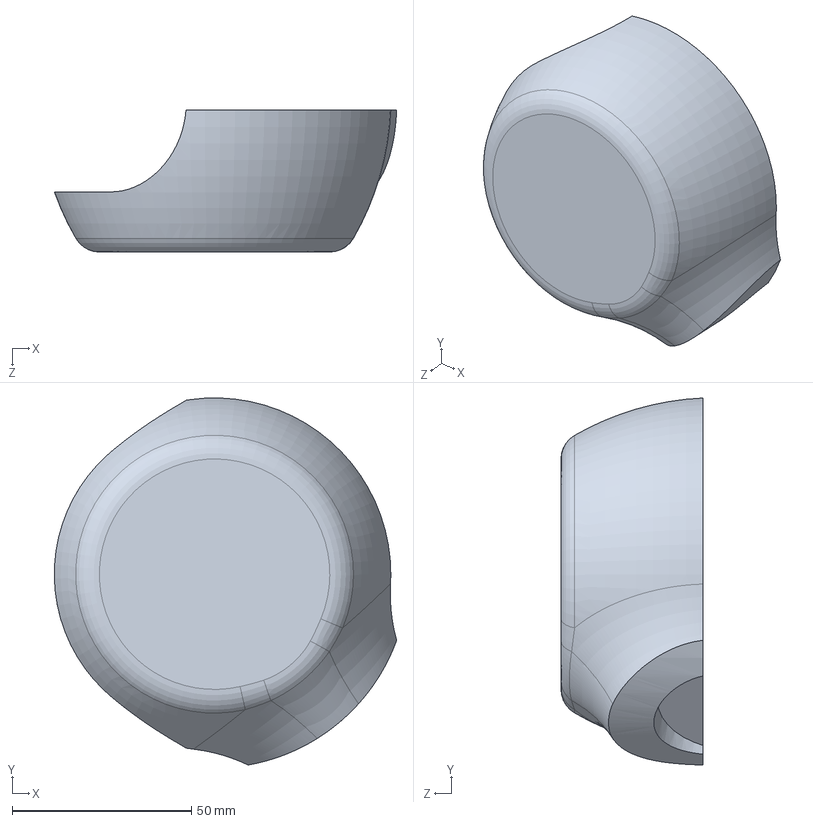
[picture p71: CAD file, 2023-09-10]
design/Level 4/Inner Knee Cover.SLDPRT
95.6 x 102.4 x 39.7 mm
