Engineerabot/Cheetah/design/Level 4/Rib4.SLDPRT

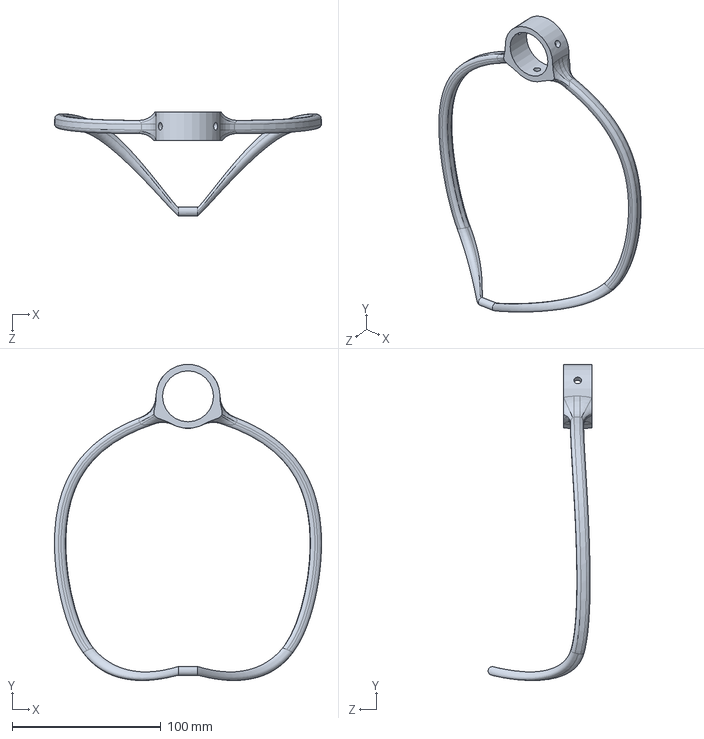
[picture p72: CAD file, 2023-09-10]
design/Level 4/Rib4.SLDPRT
179.8 x 212.8 x 69.8 mm
