Engineerabot/Cheetah/design/Level 4/Rib5.SLDPRT

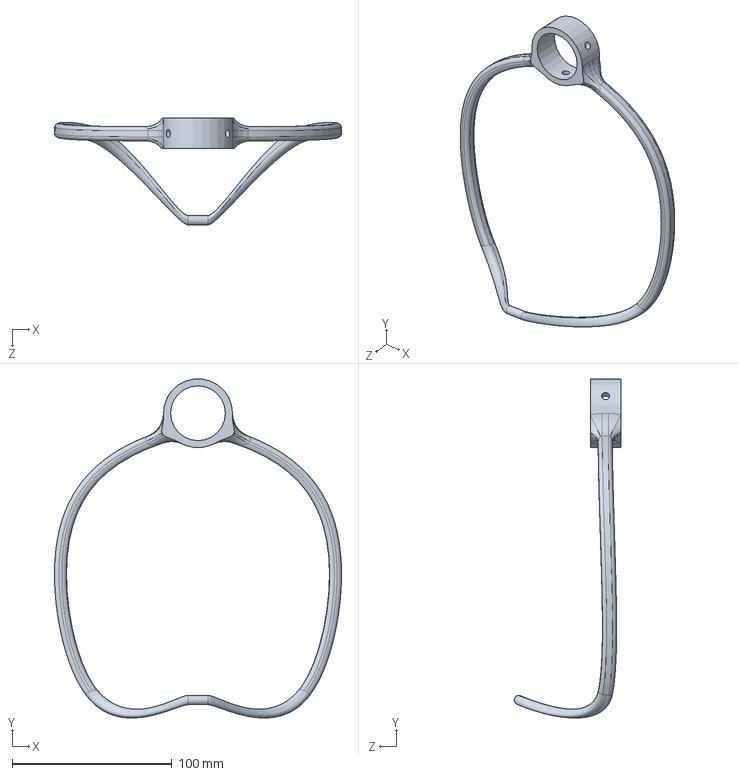
[picture p73: CAD file, 2023-09-10]
design/Level 4/Rib5.SLDPRT
179.7 x 212.2 x 66.7 mm
