Engineerabot/Cheetah/design/Level 4/Sternum.SLDPRT

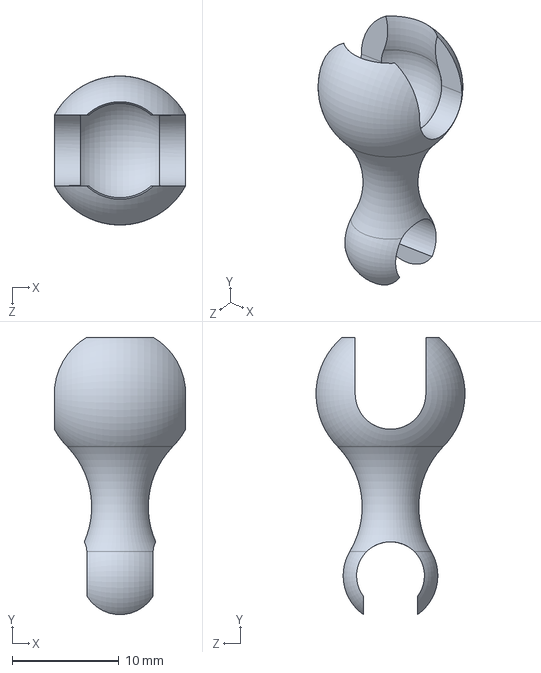
[picture p74: CAD file, 2023-09-10]
design/Level 4/Sternum.SLDPRT
12.3 x 25.9 x 14.0 mm
