Engineerabot/Cheetah/design/Level 4/Spine.SLDPRT

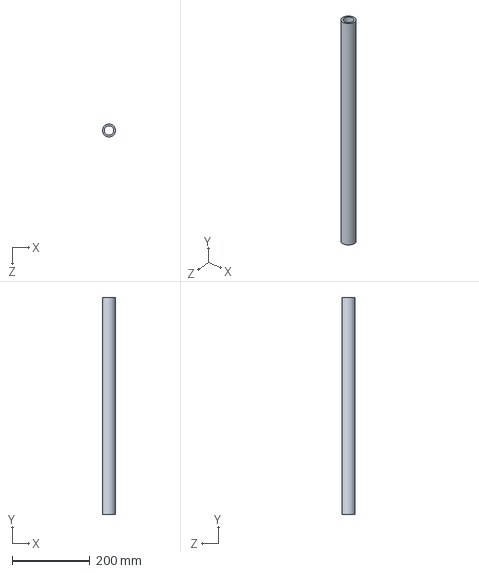
[picture p75: CAD file, 2023-09-10]
design/Level 4/Spine.SLDPRT
33.4 x 558.8 x 33.4 mm
