Engineerabot/Cheetah/design/Level 4/Knee Bar.SLDPRT

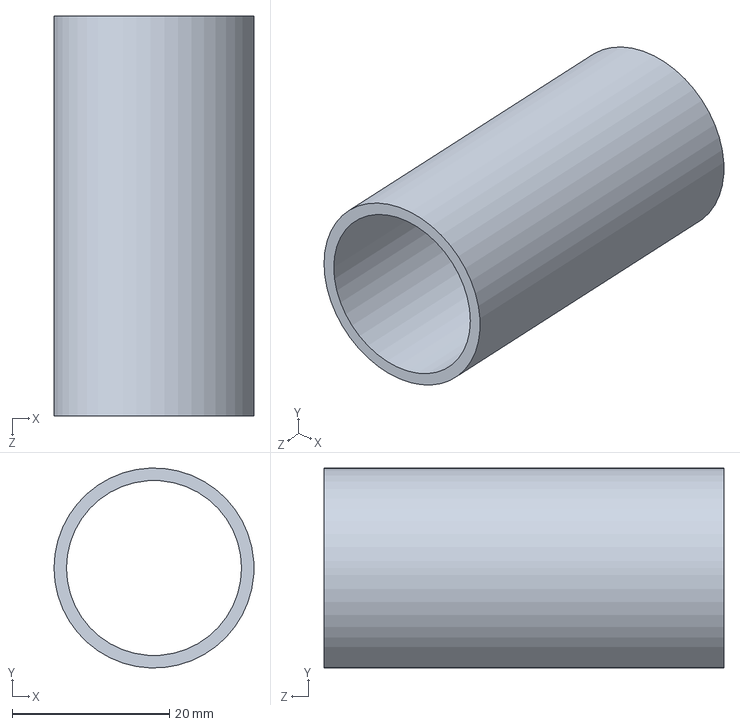
[picture p76: CAD file, 2023-09-10]
design/Level 4/Knee Bar.SLDPRT
25.4 x 25.4 x 50.8 mm
