Engineerabot/Cheetah/design/Level 4/Rib11.SLDPRT

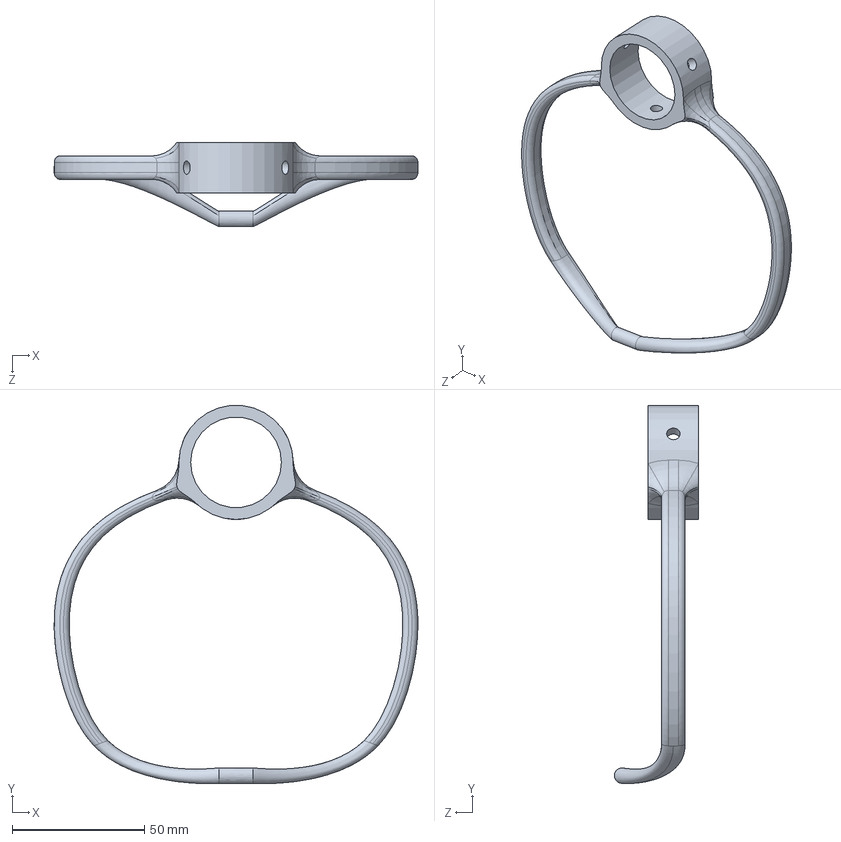
[picture p77: CAD file, 2023-09-10]
design/Level 4/Rib11.SLDPRT
137.4 x 142.8 x 31.8 mm
