Engineerabot/Cheetah/design/Level 4/Humerus.SLDPRT

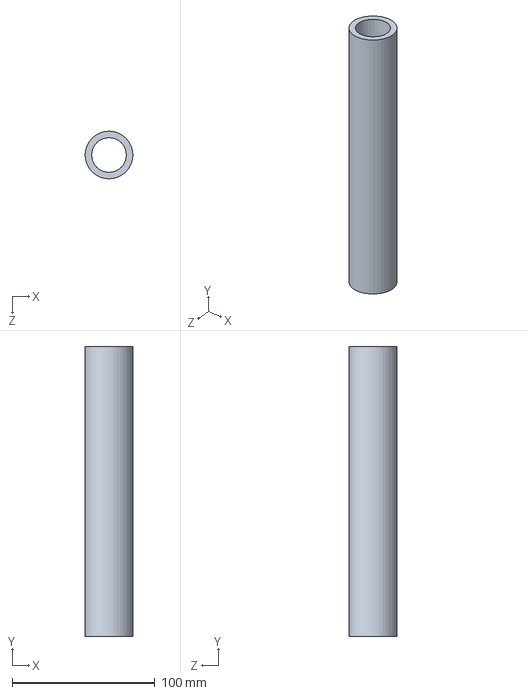
[picture p78: CAD file, 2023-09-10]
design/Level 4/Humerus.SLDPRT
33.3 x 203.2 x 33.4 mm
