Engineerabot/Cheetah/design/Level 4/Inner Knee.SLDPRT

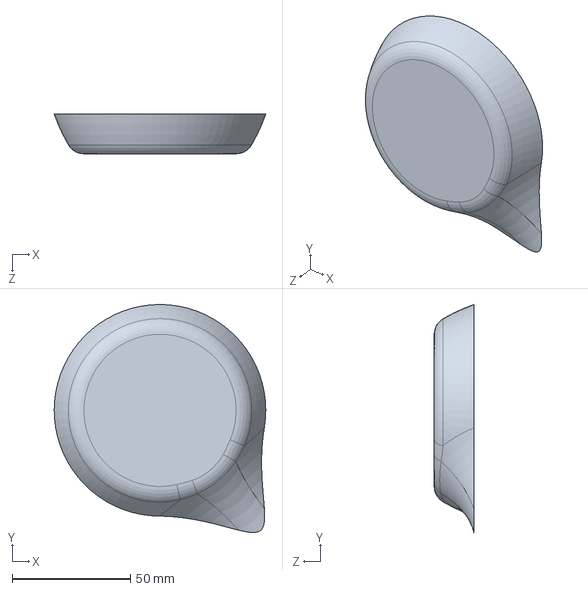
[picture p79: CAD file, 2023-09-10]
design/Level 4/Inner Knee.SLDPRT
89.5 x 96.4 x 16.8 mm
