Engineerabot/Cheetah/design/Level 4/Rib6.SLDPRT

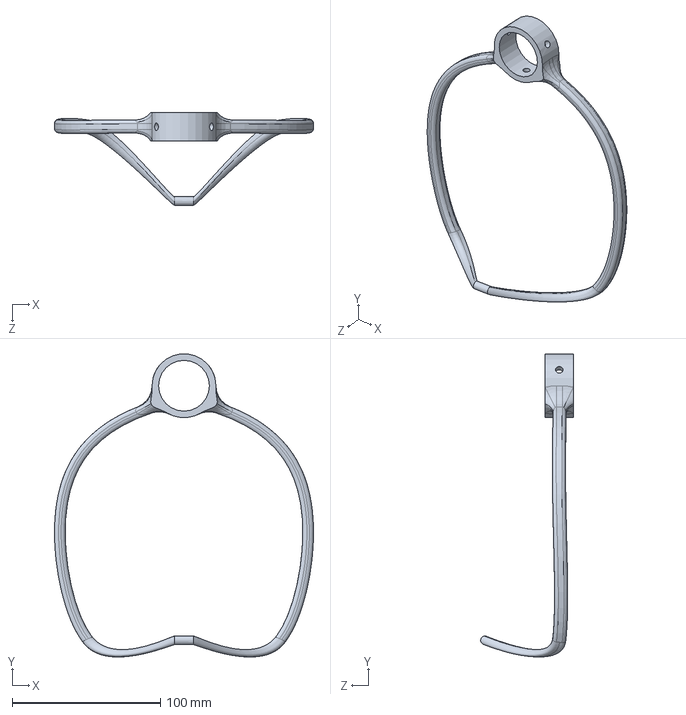
[picture p80: CAD file, 2023-09-10]
design/Level 4/Rib6.SLDPRT
174.9 x 204.6 x 62.6 mm
