Engineerabot/Cheetah/design/Level 4/Rib10.SLDPRT

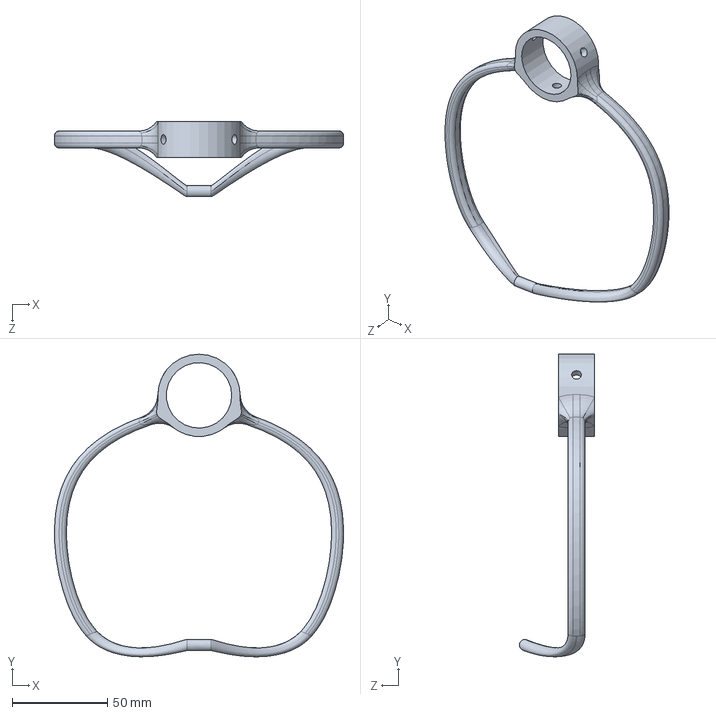
[picture p81: CAD file, 2023-09-10]
design/Level 4/Rib10.SLDPRT
151.4 x 158.6 x 39.5 mm
