Engineerabot/Cheetah/design/Level 4/Inner Knee Joint.SLDPRT

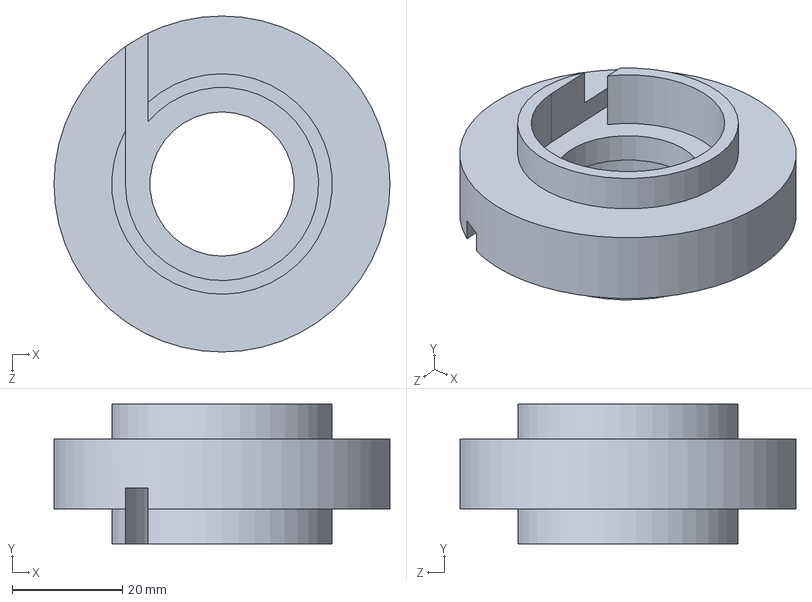
[picture p82: CAD file, 2023-09-10]
design/Level 4/Inner Knee Joint.SLDPRT
61.0 x 25.4 x 61.0 mm
