Engineerabot/Cheetah/design/Level 4/Knee Cap.SLDPRT

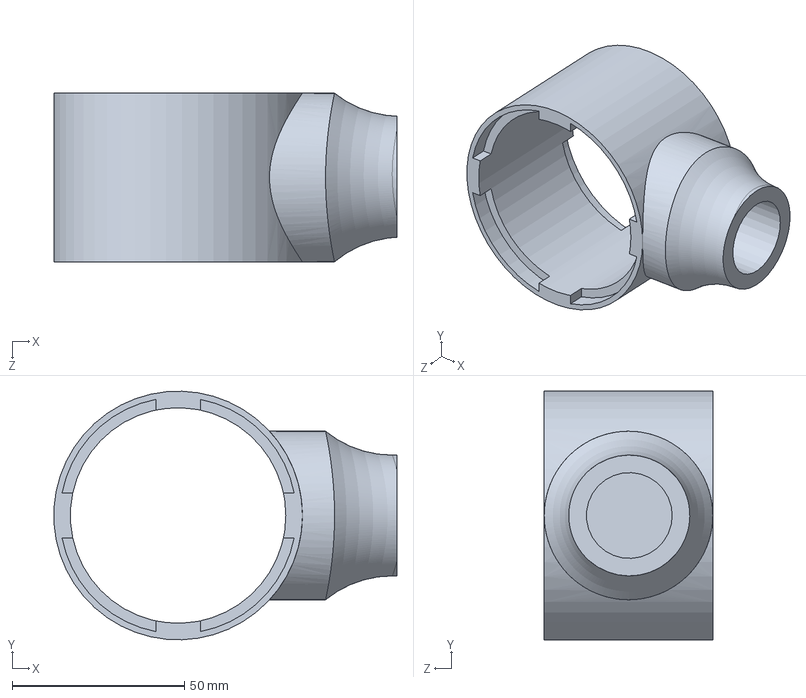
[picture p83: CAD file, 2023-09-10]
design/Level 4/Knee Cap.SLDPRT
99.5 x 72.1 x 48.9 mm
