Engineerabot/Cheetah/design/Level 4/Inner Neck Joint.SLDPRT

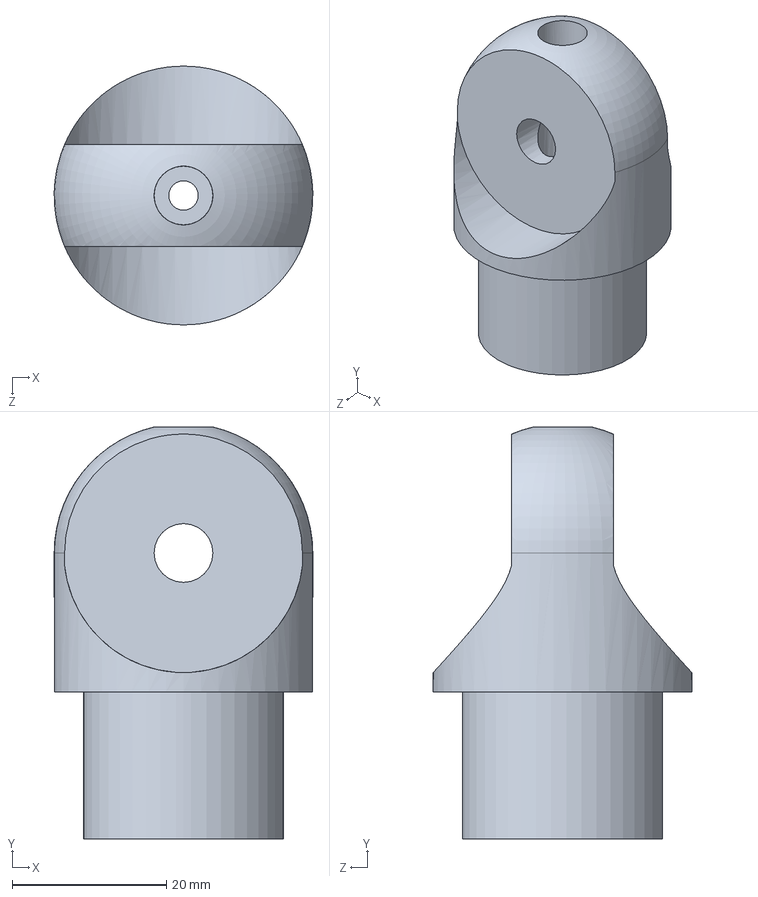
[picture p84: CAD file, 2023-09-10]
design/Level 4/Inner Neck Joint.SLDPRT
33.5 x 53.4 x 33.5 mm
