Engineerabot/Cheetah/design/Level 4/Outer Elbow Joint.SLDPRT

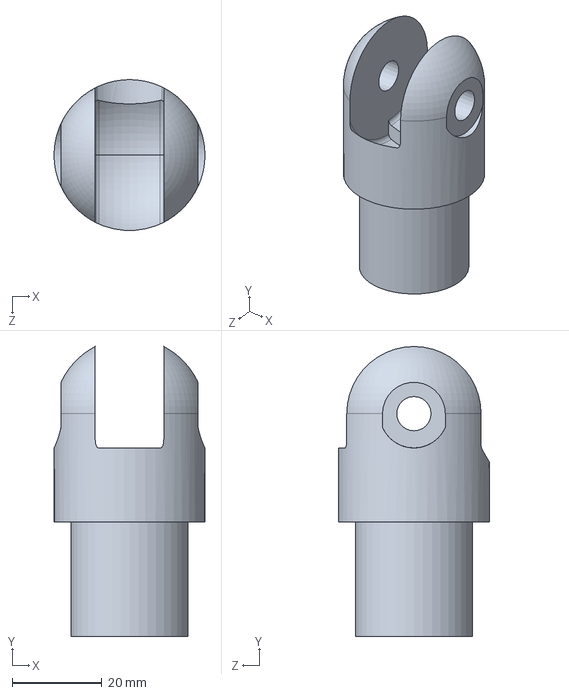
[picture p85: CAD file, 2022-10-15]
design/Level 4/Outer Elbow Joint.SLDPRT
33.5 x 64.5 x 33.5 mm
