Engineerabot/Cheetah/design/Level 4/Outer Tail Joint.SLDPRT

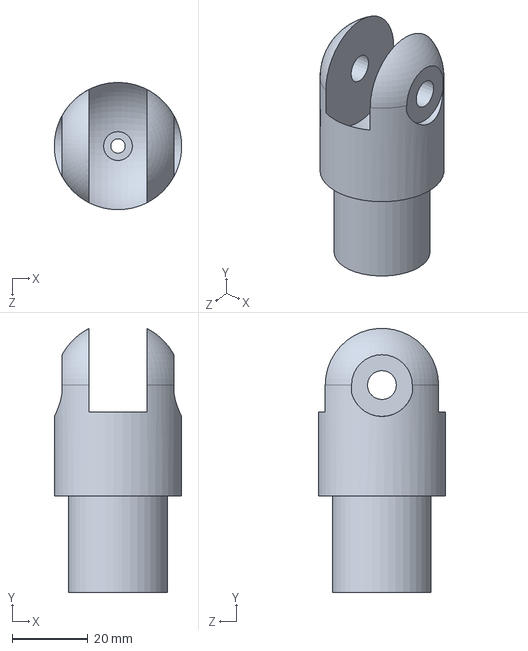
[picture p86: CAD file, 2022-10-08]
design/Level 4/Outer Tail Joint.SLDPRT
33.5 x 69.5 x 33.5 mm
