Engineerabot/Cheetah/design/Level 4/Upper Pelvis.SLDPRT

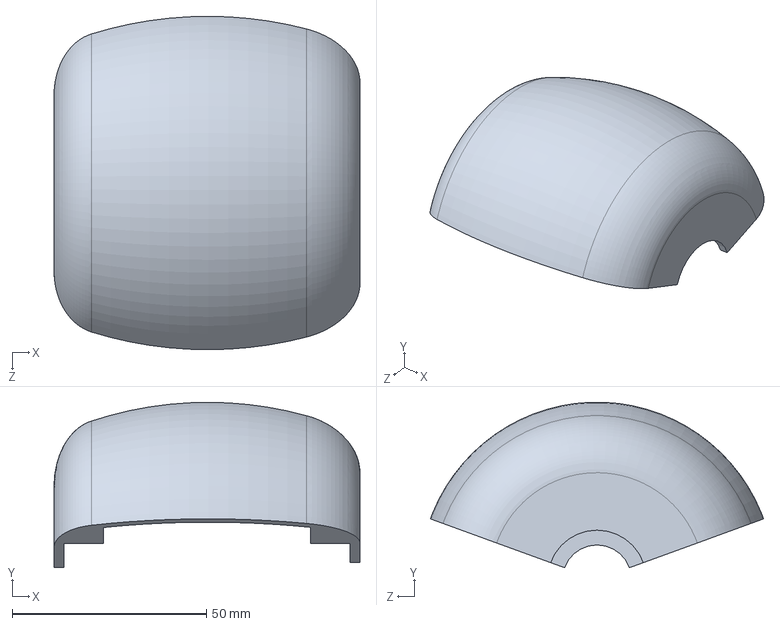
[picture p87: CAD file, 2022-09-11]
design/Level 4/Upper Pelvis.SLDPRT
78.7 x 42.6 x 85.8 mm
