Engineerabot/Cheetah/design/Level 3/Inner Knee Joint.SLDASM

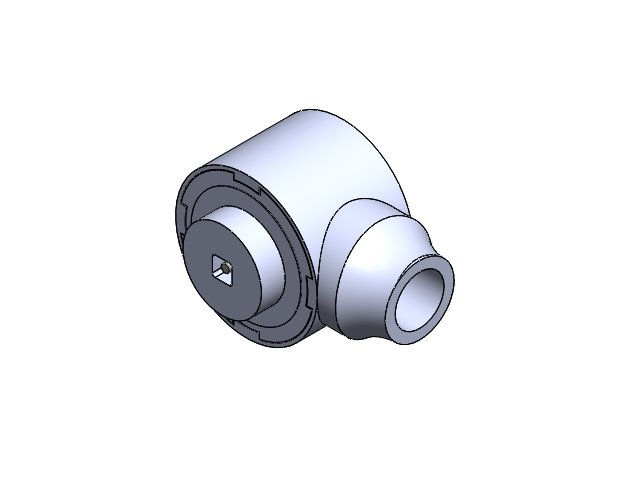
[picture p89: CAD file, 2023-09-10]
design/Level 3/Inner Knee Joint.SLDASM
Knee Cap
Inner Knee Cap
9271K662_Torsion Spring x 2
6908-2RS-EZO x 2
Knee Bar
32 RPM Premium Gear Motor
KneeShaftCollar
Outer Knee Cap
Inner Knee Joint
