Engineerabot/Cheetah/design/Level 2/Hind Leg Mechanics - Left.SLDASM

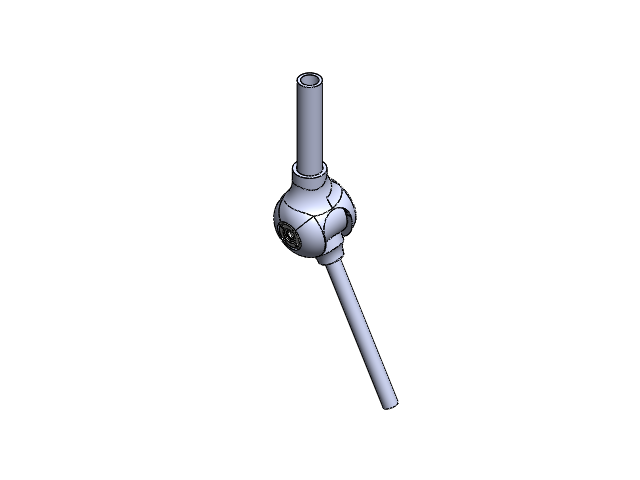
[picture p90: CAD file, 2023-09-10]
design/Level 2/Hind Leg Mechanics - Left.SLDASM
Femur
Upper Left Knee
6597K21_Rotary Speed Limiter
6908-2RS-EZO x 3
Knee Cap
Inner Knee Cap
9271K662_Torsion Spring x 2
Knee Bar
32 RPM Premium Gear Motor
KneeShaftCollar
Outer Knee Cap
Inner Knee Joint
Inner Left Knee Cover
Tibia
