Engineerabot/Cheetah/design/Level 3/Knee Joint.SLDASM

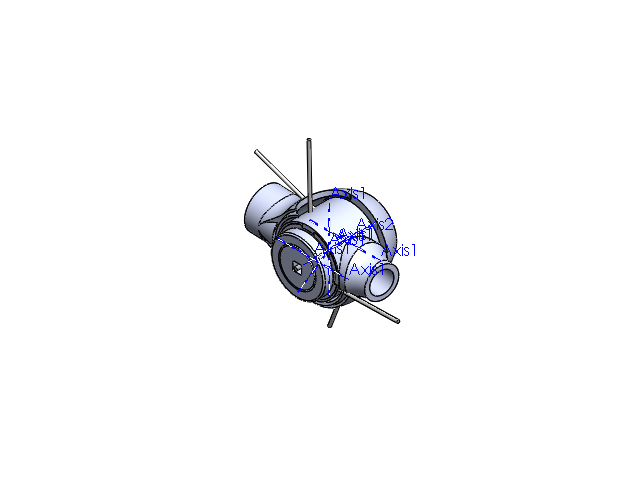
[picture p92: CAD file, 2023-09-10]
design/Level 3/Knee Joint.SLDASM
Inner Knee Cap
Knee Bar
Inner Knee Joint
6908-2RS-EZO x 4
Outer Knee Cap
Knee Cap
6597K21_Rotary Speed Limiter
9271K662_Torsion Spring x 2
32 RPM Premium Gear Motor
Upper Left Knee
